Takazudo/zudo-blanks/panels/art-kumiko-void/alternatives/standard/README.md

# Kumiko Void — Standard Alternative

These nine boards form the complete standard Kumiko alternative to the selected wide set in the parent directory. Replace all nine layers together; do not mix standard and wide layers.

The original board IDs are preserved. Color and ENIG sequence match the wide set. This directory is not an instruction to build an additional stack.

| Layer | Original board ID | Mask | Finish |
| ---: | --- | --- | --- |
| 1 | 17-kumiko-void-standard-L01-black-enig-art | black | enig-art |
| 2 | 17-kumiko-void-standard-L02-red-mask-only | red | mask-only |
| 3 | 17-kumiko-void-standard-L03-green-mask-only | green | mask-only |
| 4 | 17-kumiko-void-standard-L04-black-enig-art | black | enig-art |
| 5 | 17-kumiko-void-standard-L05-red-mask-only | red | mask-only |
| 6 | 17-kumiko-void-standard-L06-green-mask-only | green | mask-only |
| 7 | 17-kumiko-void-standard-L07-black-enig-art | black | enig-art |
| 8 | 17-kumiko-void-standard-L08-red-mask-only | red | mask-only |
| 9 | 17-kumiko-void-standard-L09-green-mask-only | green | mask-only |

These files are editable handoff boards. KiCad DRC/CAM, supplier acceptance, quote, and physical-fit checks remain pending.
