Takazudo/zudo-blanks/doc/src/content/docs/catalog/index.mdx

---
title: Panel Catalog
description: Every panel project in the repository, with a source-derived preview.
sidebar_position: 1
---

Browse all 66 panel project directories. Each image is a **KiCad layer rendering** of the committed board source. It is a visual directory aid, not a supplier CAM approval. The five new layered designs and grouped lower packages show every selected board or sheet; open their design pages for the Revision 5 visual concept, interactive 3D preview and fabrication records.

**Release boundary:** Local native DRC and CAM checks cover the five new stacks and grouped lower sheets. Factory CAM review, quotes, finish availability and physical fit remain pending. No purchase or factory acceptance is recorded.

[Five layered designs](../designs/) · [Manufacturing records](../manufacturing/) · [Preview regeneration](../workflow/panel-previews)

## Plain blanks and adapters

20 project directories.

<div className="panel-grid">
<article className="panel-card">
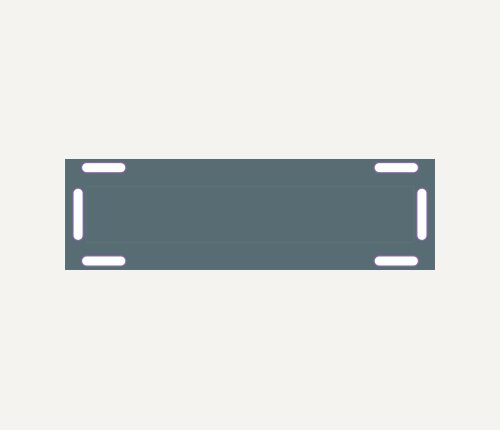
[picture p9: doc/public/assets/panels/alumi-3u-to-1u-v1.png]
KiCad source rendering of Alumi 3U To 1U V1

<h3><a href="https://github.com/Takazudo/zudo-blanks/tree/main/panels/alumi-3u-to-1u-v1">Alumi 3U To 1U V1</a></h3>
<p>Repository design · manufacturing status not established</p>
<small><code>panels/alumi-3u-to-1u-v1</code></small>
</article>
<article className="panel-card">
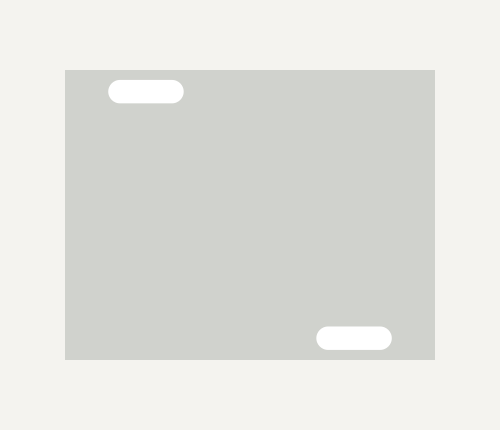
[picture p10: doc/public/assets/panels/alumi-blanks-v1-1U-10hp.png]
KiCad source rendering of Plain 1U · 10 HP

<h3><a href="https://github.com/Takazudo/zudo-blanks/tree/main/panels/alumi-blanks-v1-1U-10hp">Plain 1U · 10 HP</a></h3>
<p>Repository design · manufacturing status not established</p>
<small><code>panels/alumi-blanks-v1-1U-10hp</code></small>
</article>
<article className="panel-card">
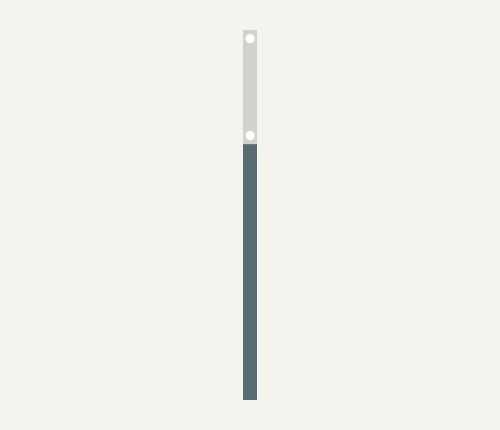
[picture p11: doc/public/assets/panels/alumi-blanks-v1-1U-1hp.png]
KiCad source rendering of Plain 1U · 1 HP

<h3><a href="https://github.com/Takazudo/zudo-blanks/tree/main/panels/alumi-blanks-v1-1U-1hp">Plain 1U · 1 HP</a></h3>
<p>Repository design · manufacturing status not established</p>
<small><code>panels/alumi-blanks-v1-1U-1hp</code></small>
</article>
<article className="panel-card">
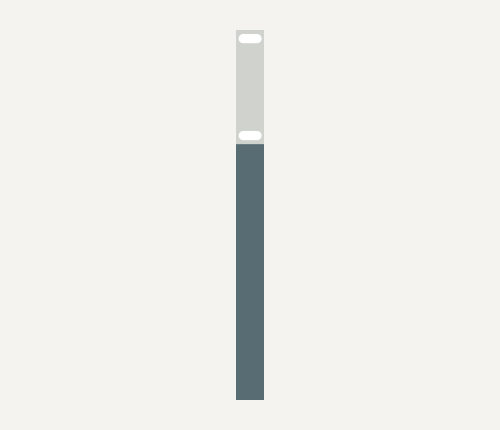
[picture p12: doc/public/assets/panels/alumi-blanks-v1-1U-2hp.png]
KiCad source rendering of Plain 1U · 2 HP

<h3><a href="https://github.com/Takazudo/zudo-blanks/tree/main/panels/alumi-blanks-v1-1U-2hp">Plain 1U · 2 HP</a></h3>
<p>Repository design · manufacturing status not established</p>
<small><code>panels/alumi-blanks-v1-1U-2hp</code></small>
</article>
<article className="panel-card">
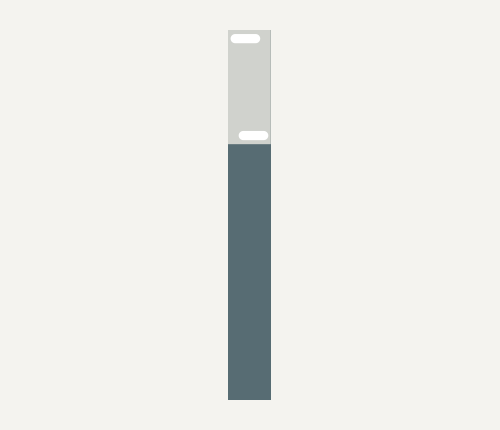
[picture p13: doc/public/assets/panels/alumi-blanks-v1-1U-3hp.png]
KiCad source rendering of Plain 1U · 3 HP

<h3><a href="https://github.com/Takazudo/zudo-blanks/tree/main/panels/alumi-blanks-v1-1U-3hp">Plain 1U · 3 HP</a></h3>
<p>Repository design · manufacturing status not established</p>
<small><code>panels/alumi-blanks-v1-1U-3hp</code></small>
</article>
<article className="panel-card">
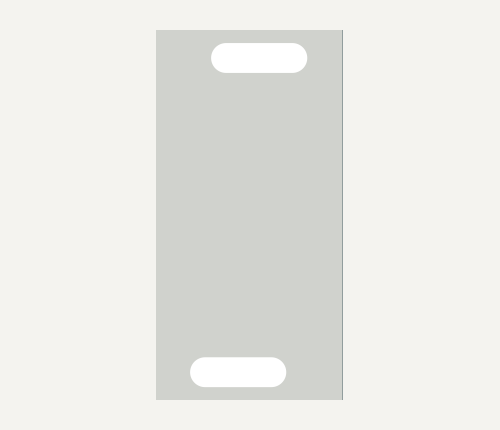
[picture p14: doc/public/assets/panels/alumi-blanks-v1-1U-4hp.png]
KiCad source rendering of Plain 1U · 4 HP

<h3><a href="https://github.com/Takazudo/zudo-blanks/tree/main/panels/alumi-blanks-v1-1U-4hp">Plain 1U · 4 HP</a></h3>
<p>Repository design · manufacturing status not established</p>
<small><code>panels/alumi-blanks-v1-1U-4hp</code></small>
</article>
<article className="panel-card">
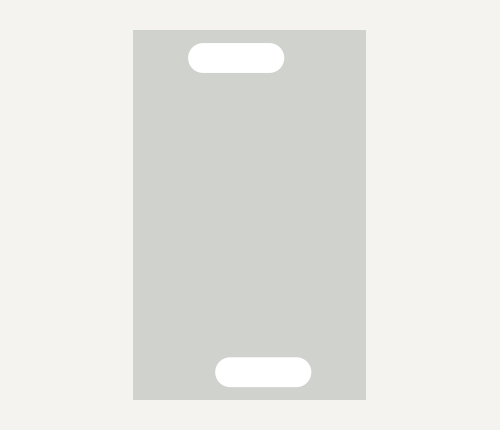
[picture p15: doc/public/assets/panels/alumi-blanks-v1-1U-5hp.png]
KiCad source rendering of Plain 1U · 5 HP

<h3><a href="https://github.com/Takazudo/zudo-blanks/tree/main/panels/alumi-blanks-v1-1U-5hp">Plain 1U · 5 HP</a></h3>
<p>Repository design · manufacturing status not established</p>
<small><code>panels/alumi-blanks-v1-1U-5hp</code></small>
</article>
<article className="panel-card">
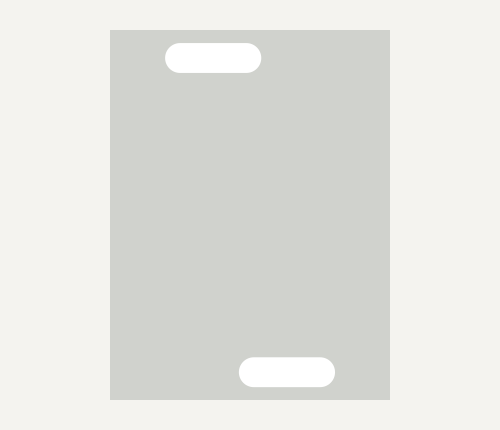
[picture p16: doc/public/assets/panels/alumi-blanks-v1-1U-6hp.png]
KiCad source rendering of Plain 1U · 6 HP

<h3><a href="https://github.com/Takazudo/zudo-blanks/tree/main/panels/alumi-blanks-v1-1U-6hp">Plain 1U · 6 HP</a></h3>
<p>Repository design · manufacturing status not established</p>
<small><code>panels/alumi-blanks-v1-1U-6hp</code></small>
</article>
<article className="panel-card">
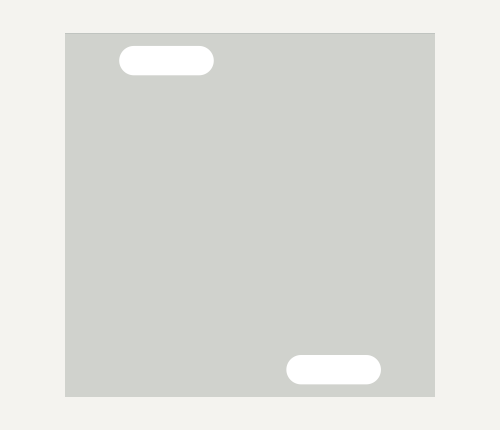
[picture p17: doc/public/assets/panels/alumi-blanks-v1-1U-8hp.png]
KiCad source rendering of Plain 1U · 8 HP

<h3><a href="https://github.com/Takazudo/zudo-blanks/tree/main/panels/alumi-blanks-v1-1U-8hp">Plain 1U · 8 HP</a></h3>
<p>Repository design · manufacturing status not established</p>
<small><code>panels/alumi-blanks-v1-1U-8hp</code></small>
</article>
<article className="panel-card">
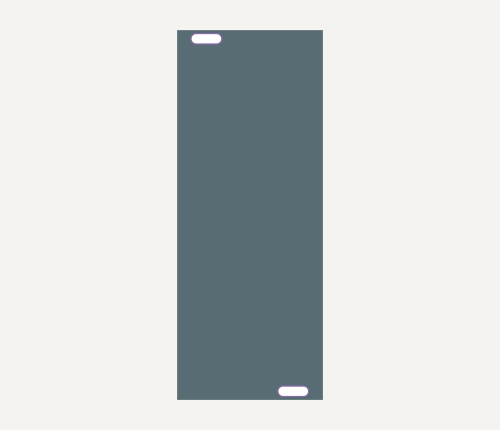
[picture p18: doc/public/assets/panels/alumi-blanks-v1-3U-10hp.png]
KiCad source rendering of Plain 3U · 10 HP

<h3><a href="https://github.com/Takazudo/zudo-blanks/tree/main/panels/alumi-blanks-v1-3U-10hp">Plain 3U · 10 HP</a></h3>
<p>Repository design · manufacturing status not established</p>
<small><code>panels/alumi-blanks-v1-3U-10hp</code></small>
</article>
<article className="panel-card">
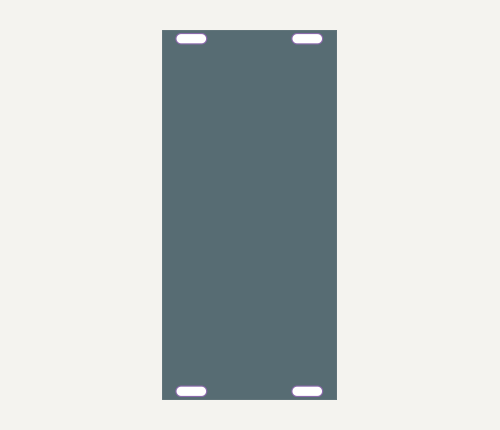
[picture p19: doc/public/assets/panels/alumi-blanks-v1-3U-12hp.png]
KiCad source rendering of Plain 3U · 12 HP

<h3><a href="https://github.com/Takazudo/zudo-blanks/tree/main/panels/alumi-blanks-v1-3U-12hp">Plain 3U · 12 HP</a></h3>
<p>Repository design · manufacturing status not established</p>
<small><code>panels/alumi-blanks-v1-3U-12hp</code></small>
</article>
<article className="panel-card">
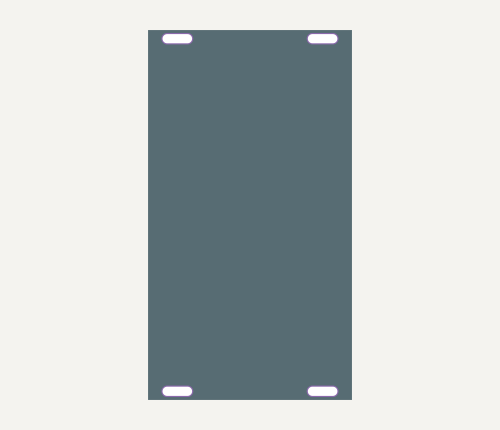
[picture p20: doc/public/assets/panels/alumi-blanks-v1-3U-14hp.png]
KiCad source rendering of Plain 3U · 14 HP

<h3><a href="https://github.com/Takazudo/zudo-blanks/tree/main/panels/alumi-blanks-v1-3U-14hp">Plain 3U · 14 HP</a></h3>
<p>Repository design · manufacturing status not established</p>
<small><code>panels/alumi-blanks-v1-3U-14hp</code></small>
</article>
<article className="panel-card">
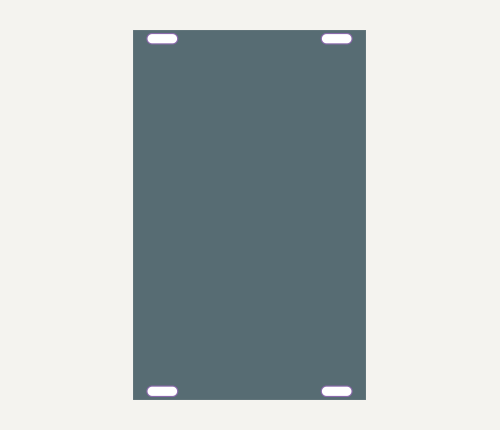
[picture p21: doc/public/assets/panels/alumi-blanks-v1-3U-16hp.png]
KiCad source rendering of Plain 3U · 16 HP

<h3><a href="https://github.com/Takazudo/zudo-blanks/tree/main/panels/alumi-blanks-v1-3U-16hp">Plain 3U · 16 HP</a></h3>
<p>Repository design · manufacturing status not established</p>
<small><code>panels/alumi-blanks-v1-3U-16hp</code></small>
</article>
<article className="panel-card">
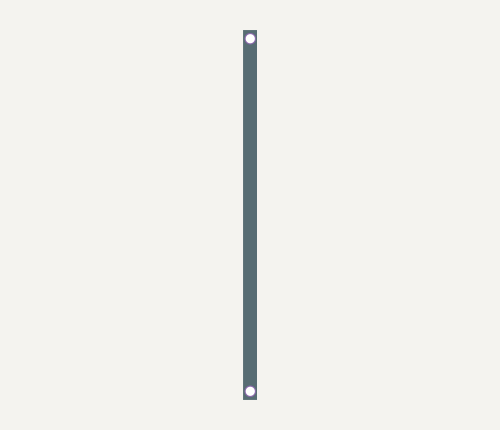
[picture p22: doc/public/assets/panels/alumi-blanks-v1-3U-1hp.png]
KiCad source rendering of Plain 3U · 1 HP

<h3><a href="https://github.com/Takazudo/zudo-blanks/tree/main/panels/alumi-blanks-v1-3U-1hp">Plain 3U · 1 HP</a></h3>
<p>Repository design · manufacturing status not established</p>
<small><code>panels/alumi-blanks-v1-3U-1hp</code></small>
</article>
<article className="panel-card">
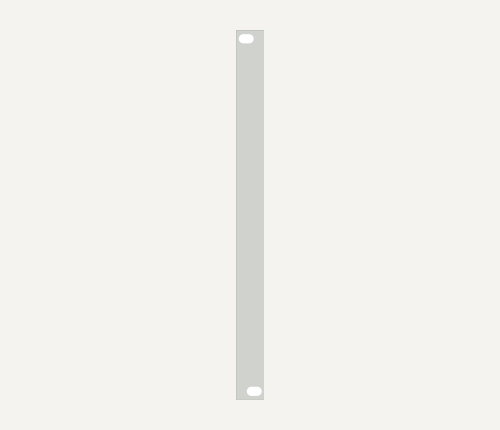
[picture p23: doc/public/assets/panels/alumi-blanks-v1-3U-2hp.png]
KiCad source rendering of Plain 3U · 2 HP

<h3><a href="https://github.com/Takazudo/zudo-blanks/tree/main/panels/alumi-blanks-v1-3U-2hp">Plain 3U · 2 HP</a></h3>
<p>Repository design · manufacturing status not established</p>
<small><code>panels/alumi-blanks-v1-3U-2hp</code></small>
</article>
<article className="panel-card">
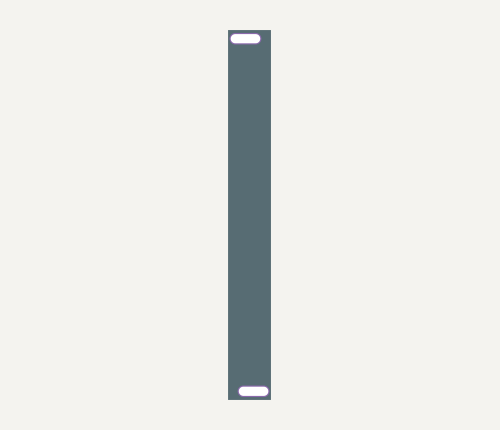
[picture p24: doc/public/assets/panels/alumi-blanks-v1-3U-3hp.png]
KiCad source rendering of Plain 3U · 3 HP

<h3><a href="https://github.com/Takazudo/zudo-blanks/tree/main/panels/alumi-blanks-v1-3U-3hp">Plain 3U · 3 HP</a></h3>
<p>Repository design · manufacturing status not established</p>
<small><code>panels/alumi-blanks-v1-3U-3hp</code></small>
</article>
<article className="panel-card">
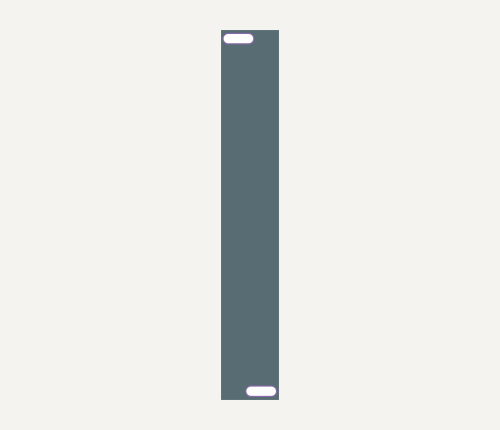
[picture p25: doc/public/assets/panels/alumi-blanks-v1-3U-4hp.png]
KiCad source rendering of Plain 3U · 4 HP

<h3><a href="https://github.com/Takazudo/zudo-blanks/tree/main/panels/alumi-blanks-v1-3U-4hp">Plain 3U · 4 HP</a></h3>
<p>Repository design · manufacturing status not established</p>
<small><code>panels/alumi-blanks-v1-3U-4hp</code></small>
</article>
<article className="panel-card">
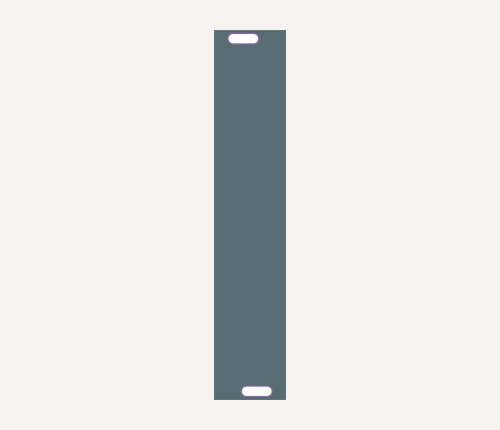
[picture p26: doc/public/assets/panels/alumi-blanks-v1-3U-5hp.png]
KiCad source rendering of Plain 3U · 5 HP

<h3><a href="https://github.com/Takazudo/zudo-blanks/tree/main/panels/alumi-blanks-v1-3U-5hp">Plain 3U · 5 HP</a></h3>
<p>Repository design · manufacturing status not established</p>
<small><code>panels/alumi-blanks-v1-3U-5hp</code></small>
</article>
<article className="panel-card">
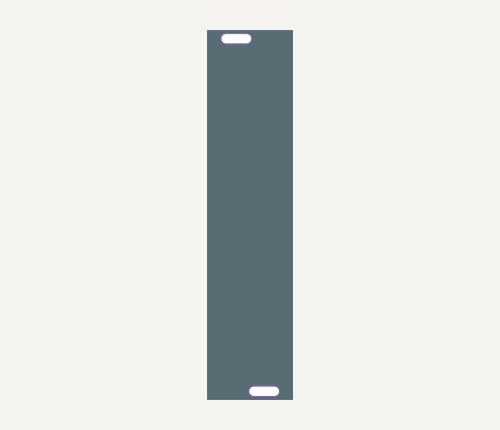
[picture p27: doc/public/assets/panels/alumi-blanks-v1-3U-6hp.png]
KiCad source rendering of Plain 3U · 6 HP

<h3><a href="https://github.com/Takazudo/zudo-blanks/tree/main/panels/alumi-blanks-v1-3U-6hp">Plain 3U · 6 HP</a></h3>
<p>Repository design · manufacturing status not established</p>
<small><code>panels/alumi-blanks-v1-3U-6hp</code></small>
</article>
<article className="panel-card">
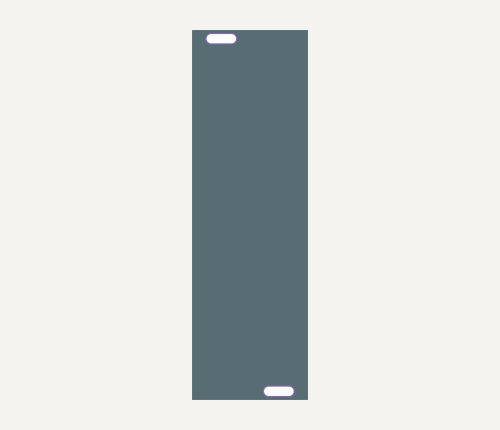
[picture p28: doc/public/assets/panels/alumi-blanks-v1-3U-8hp.png]
KiCad source rendering of Plain 3U · 8 HP

<h3><a href="https://github.com/Takazudo/zudo-blanks/tree/main/panels/alumi-blanks-v1-3U-8hp">Plain 3U · 8 HP</a></h3>
<p>Repository design · manufacturing status not established</p>
<small><code>panels/alumi-blanks-v1-3U-8hp</code></small>
</article>
</div>

## Side frames

5 project directories.

<div className="panel-grid">
<article className="panel-card">
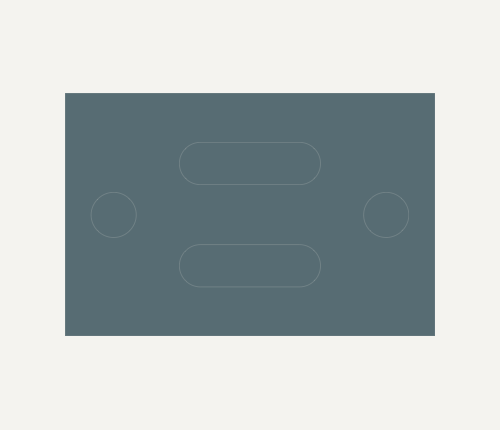
[picture p29: doc/public/assets/panels/zb-side-frame-1u.png]
KiCad source rendering of Zb Side Frame 1U

<h3><a href="https://github.com/Takazudo/zudo-blanks/tree/main/panels/zb-side-frame-1u">Zb Side Frame 1U</a></h3>
<p>Repository design · manufacturing status not established</p>
<small><code>panels/zb-side-frame-1u</code></small>
</article>
<article className="panel-card">
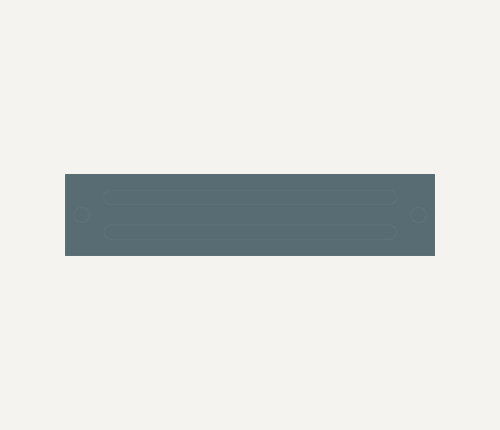
[picture p30: doc/public/assets/panels/zb-side-frame-3u.png]
KiCad source rendering of Zb Side Frame 3U

<h3><a href="https://github.com/Takazudo/zudo-blanks/tree/main/panels/zb-side-frame-3u">Zb Side Frame 3U</a></h3>
<p>Repository design · manufacturing status not established</p>
<small><code>panels/zb-side-frame-3u</code></small>
</article>
<article className="panel-card">
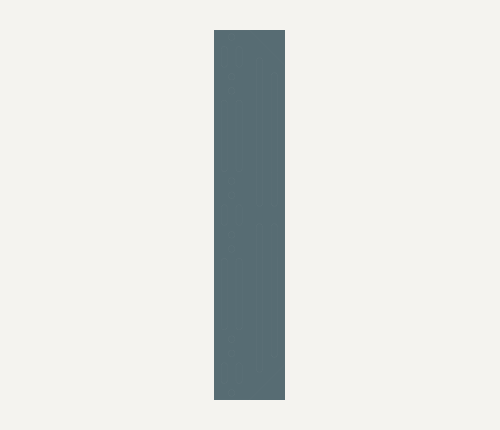
[picture p31: doc/public/assets/panels/zb-side-frame-7u.png]
KiCad source rendering of Zb Side Frame 7U

<h3><a href="https://github.com/Takazudo/zudo-blanks/tree/main/panels/zb-side-frame-7u">Zb Side Frame 7U</a></h3>
<p>Repository design · manufacturing status not established</p>
<small><code>panels/zb-side-frame-7u</code></small>
</article>
<article className="panel-card">
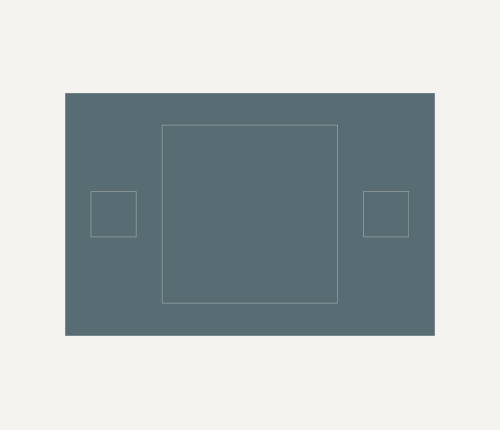
[picture p32: doc/public/assets/panels/zb-side-frame-pad-1u.png]
KiCad source rendering of Zb Side Frame Pad 1U

<h3><a href="https://github.com/Takazudo/zudo-blanks/tree/main/panels/zb-side-frame-pad-1u">Zb Side Frame Pad 1U</a></h3>
<p>Repository design · manufacturing status not established</p>
<small><code>panels/zb-side-frame-pad-1u</code></small>
</article>
<article className="panel-card">
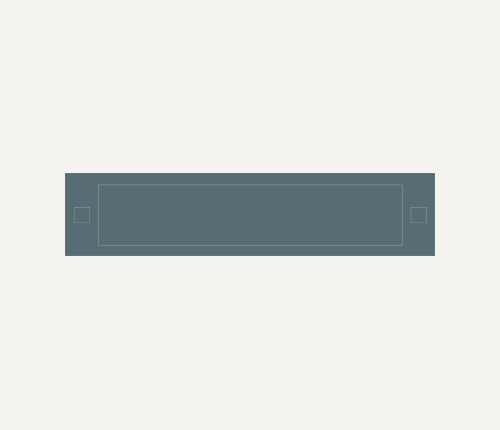
[picture p33: doc/public/assets/panels/zb-side-frame-pad-3u.png]
KiCad source rendering of Zb Side Frame Pad 3U

<h3><a href="https://github.com/Takazudo/zudo-blanks/tree/main/panels/zb-side-frame-pad-3u">Zb Side Frame Pad 3U</a></h3>
<p>Repository design · manufacturing status not established</p>
<small><code>panels/zb-side-frame-pad-3u</code></small>
</article>
</div>

## Artwork and layered designs

11 project directories.

<div className="panel-grid">
<article className="panel-card">
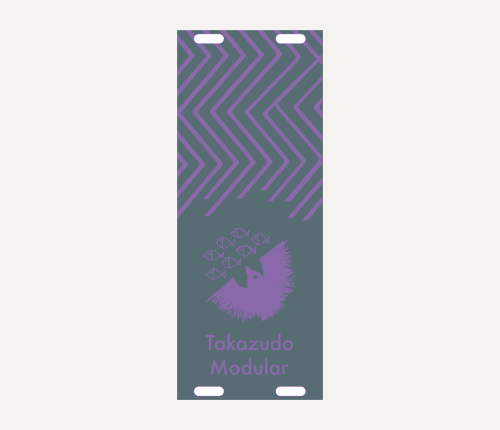
[picture p34: doc/public/assets/panels/art-10hp-takazudo-modular.png]
KiCad source rendering of 10Hp Takazudo Modular

<h3><a href="https://github.com/Takazudo/zudo-blanks/tree/main/panels/art-10hp-takazudo-modular">10Hp Takazudo Modular</a></h3>
<p>Repository design · manufacturing status not established</p>
<small><code>panels/art-10hp-takazudo-modular</code></small>
</article>
<article className="panel-card">
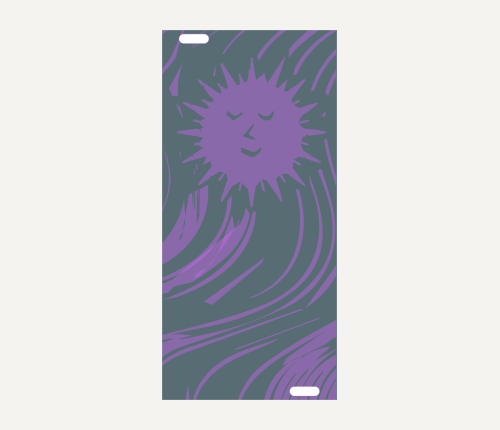
[picture p35: doc/public/assets/panels/art-12hp-sun.png]
KiCad source rendering of 12Hp Sun

<h3><a href="https://github.com/Takazudo/zudo-blanks/tree/main/panels/art-12hp-sun">12Hp Sun</a></h3>
<p>Repository design · manufacturing status not established</p>
<small><code>panels/art-12hp-sun</code></small>
</article>
<article className="panel-card">
<a href="https://github.com/Takazudo/zudo-blanks/tree/main/panels/art-coral-vault">KiCad source rendering of Coral Vault</a>
<h3><a href="https://github.com/Takazudo/zudo-blanks/tree/main/panels/art-coral-vault">Coral Vault</a></h3>
<p>8 selected layers · local native DRC/CAM checked · factory review pending</p>
<small><code>panels/art-coral-vault</code></small>
</article>
<article className="panel-card">
<a href="https://github.com/Takazudo/zudo-blanks/tree/main/panels/art-fault-line">KiCad source rendering of Fault Line</a>
<h3><a href="https://github.com/Takazudo/zudo-blanks/tree/main/panels/art-fault-line">Fault Line</a></h3>
<p>9 selected layers · local native DRC/CAM checked · factory review pending</p>
<small><code>panels/art-fault-line</code></small>
</article>
<article className="panel-card">
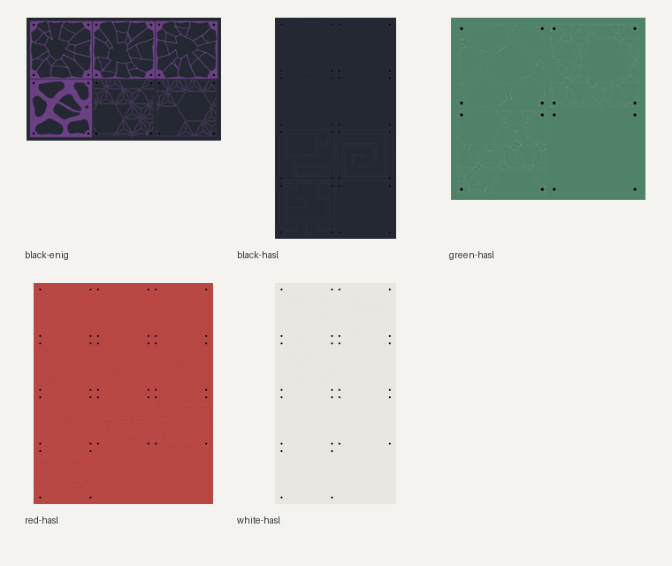
[picture p36: doc/public/assets/panels/art-grouped-lowers.png]
KiCad source rendering of Grouped Lowers

<h3><a href="https://github.com/Takazudo/zudo-blanks/tree/main/panels/art-grouped-lowers">Grouped Lowers</a></h3>
<p>5 grouped sheets · local native DRC/CAM checked · factory review pending</p>
<small><code>panels/art-grouped-lowers</code></small>
</article>
<article className="panel-card">
<a href="https://github.com/Takazudo/zudo-blanks/tree/main/panels/art-kumiko-void">KiCad source rendering of Kumiko Void</a>
<h3><a href="https://github.com/Takazudo/zudo-blanks/tree/main/panels/art-kumiko-void">Kumiko Void</a></h3>
<p>9 selected layers · local native DRC/CAM checked · factory review pending</p>
<small><code>panels/art-kumiko-void</code></small>
</article>
<article className="panel-card">
<a href="https://github.com/Takazudo/zudo-blanks/tree/main/panels/art-spider-nest">KiCad source rendering of Spider Nest</a>
<h3><a href="https://github.com/Takazudo/zudo-blanks/tree/main/panels/art-spider-nest">Spider Nest</a></h3>
<p>8 selected layers · local native DRC/CAM checked · factory review pending</p>
<small><code>panels/art-spider-nest</code></small>
</article>
<article className="panel-card">
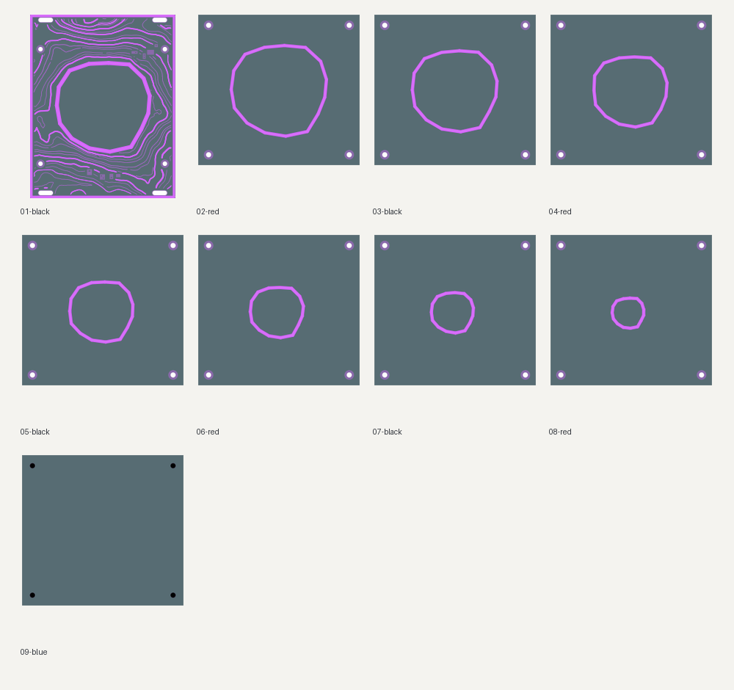
[picture p37: doc/public/assets/panels/art-strip-mine.png]
KiCad source rendering of Strip Mine

<h3><a href="https://github.com/Takazudo/zudo-blanks/tree/main/panels/art-strip-mine">Strip Mine</a></h3>
<p>9 layered source boards · historical project status</p>
<small><code>panels/art-strip-mine</code></small>
</article>
<article className="panel-card">
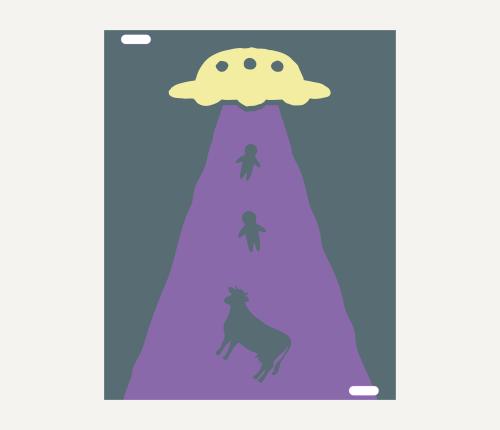
[picture p38: doc/public/assets/panels/art-ufo.png]
KiCad source rendering of Ufo

<h3><a href="https://github.com/Takazudo/zudo-blanks/tree/main/panels/art-ufo">Ufo</a></h3>
<p>Repository design · manufacturing status not established</p>
<small><code>panels/art-ufo</code></small>
</article>
<article className="panel-card">
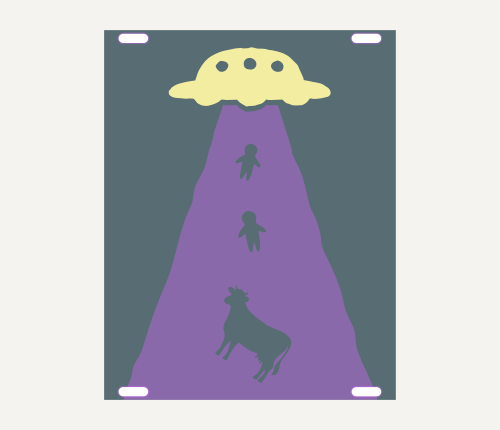
[picture p39: doc/public/assets/panels/art-ufo-v2.png]
KiCad source rendering of Ufo V2

<h3><a href="https://github.com/Takazudo/zudo-blanks/tree/main/panels/art-ufo-v2">Ufo V2</a></h3>
<p>Repository design · manufacturing status not established</p>
<small><code>panels/art-ufo-v2</code></small>
</article>
<article className="panel-card">
<a href="https://github.com/Takazudo/zudo-blanks/tree/main/panels/art-woven-maze">KiCad source rendering of Woven Maze</a>
<h3><a href="https://github.com/Takazudo/zudo-blanks/tree/main/panels/art-woven-maze">Woven Maze</a></h3>
<p>9 selected layers · local native DRC/CAM checked · factory review pending</p>
<small><code>panels/art-woven-maze</code></small>
</article>
</div>

## Saucer series

30 project directories.

<div className="panel-grid">
<article className="panel-card">
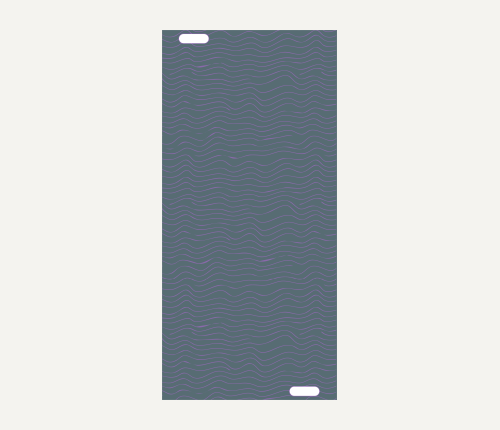
[picture p40: doc/public/assets/panels/saucer1-slow-wave-12hp.png]
KiCad source rendering of Saucer 1 · Slow Wave · 12 HP

<h3><a href="https://github.com/Takazudo/zudo-blanks/tree/main/panels/saucer1-slow-wave-12hp">Saucer 1 · Slow Wave · 12 HP</a></h3>
<p>Repository design · manufacturing status not established</p>
<small><code>panels/saucer1-slow-wave-12hp</code></small>
</article>
<article className="panel-card">
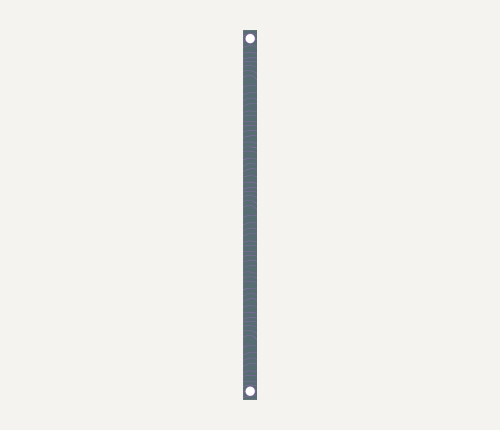
[picture p41: doc/public/assets/panels/saucer1-slow-wave-1hp.png]
KiCad source rendering of Saucer 1 · Slow Wave · 1 HP

<h3><a href="https://github.com/Takazudo/zudo-blanks/tree/main/panels/saucer1-slow-wave-1hp">Saucer 1 · Slow Wave · 1 HP</a></h3>
<p>Repository design · manufacturing status not established</p>
<small><code>panels/saucer1-slow-wave-1hp</code></small>
</article>
<article className="panel-card">
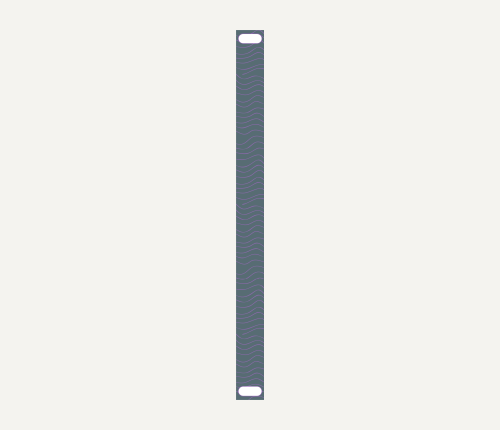
[picture p42: doc/public/assets/panels/saucer1-slow-wave-2hp.png]
KiCad source rendering of Saucer 1 · Slow Wave · 2 HP

<h3><a href="https://github.com/Takazudo/zudo-blanks/tree/main/panels/saucer1-slow-wave-2hp">Saucer 1 · Slow Wave · 2 HP</a></h3>
<p>Repository design · manufacturing status not established</p>
<small><code>panels/saucer1-slow-wave-2hp</code></small>
</article>
<article className="panel-card">
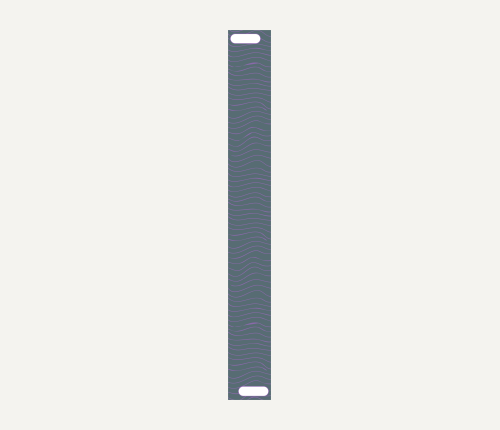
[picture p43: doc/public/assets/panels/saucer1-slow-wave-3hp.png]
KiCad source rendering of Saucer 1 · Slow Wave · 3 HP

<h3><a href="https://github.com/Takazudo/zudo-blanks/tree/main/panels/saucer1-slow-wave-3hp">Saucer 1 · Slow Wave · 3 HP</a></h3>
<p>Repository design · manufacturing status not established</p>
<small><code>panels/saucer1-slow-wave-3hp</code></small>
</article>
<article className="panel-card">
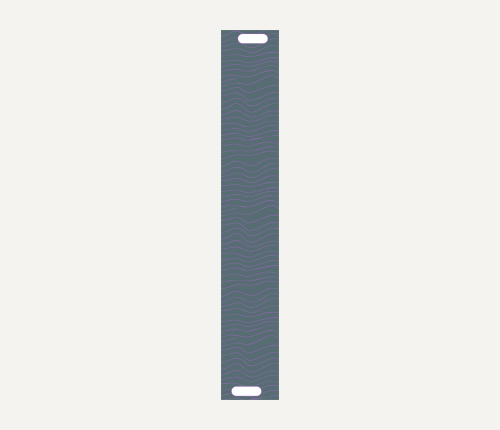
[picture p44: doc/public/assets/panels/saucer1-slow-wave-4hp.png]
KiCad source rendering of Saucer 1 · Slow Wave · 4 HP

<h3><a href="https://github.com/Takazudo/zudo-blanks/tree/main/panels/saucer1-slow-wave-4hp">Saucer 1 · Slow Wave · 4 HP</a></h3>
<p>Repository design · manufacturing status not established</p>
<small><code>panels/saucer1-slow-wave-4hp</code></small>
</article>
<article className="panel-card">
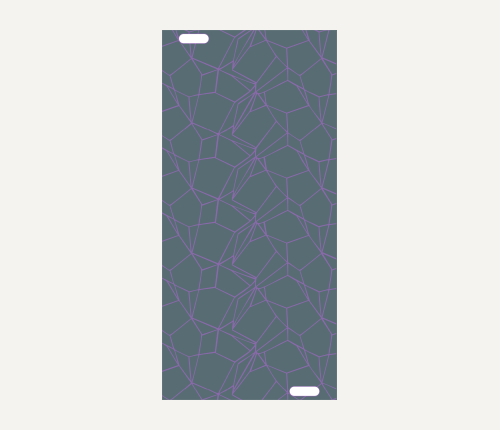
[picture p45: doc/public/assets/panels/saucer2-crystal-flow-12hp.png]
KiCad source rendering of Saucer 2 · Crystal Flow · 12 HP

<h3><a href="https://github.com/Takazudo/zudo-blanks/tree/main/panels/saucer2-crystal-flow-12hp">Saucer 2 · Crystal Flow · 12 HP</a></h3>
<p>Repository design · manufacturing status not established</p>
<small><code>panels/saucer2-crystal-flow-12hp</code></small>
</article>
<article className="panel-card">
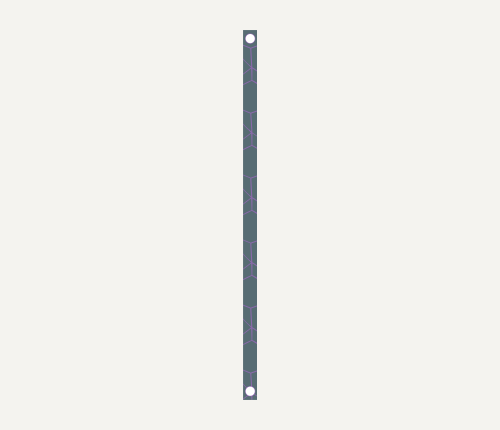
[picture p46: doc/public/assets/panels/saucer2-crystal-flow-1hp.png]
KiCad source rendering of Saucer 2 · Crystal Flow · 1 HP

<h3><a href="https://github.com/Takazudo/zudo-blanks/tree/main/panels/saucer2-crystal-flow-1hp">Saucer 2 · Crystal Flow · 1 HP</a></h3>
<p>Repository design · manufacturing status not established</p>
<small><code>panels/saucer2-crystal-flow-1hp</code></small>
</article>
<article className="panel-card">
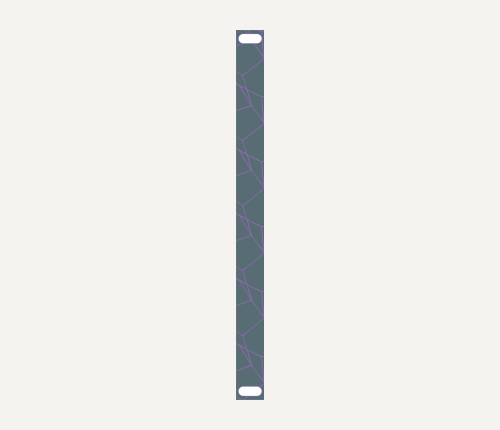
[picture p47: doc/public/assets/panels/saucer2-crystal-flow-2hp.png]
KiCad source rendering of Saucer 2 · Crystal Flow · 2 HP

<h3><a href="https://github.com/Takazudo/zudo-blanks/tree/main/panels/saucer2-crystal-flow-2hp">Saucer 2 · Crystal Flow · 2 HP</a></h3>
<p>Repository design · manufacturing status not established</p>
<small><code>panels/saucer2-crystal-flow-2hp</code></small>
</article>
<article className="panel-card">
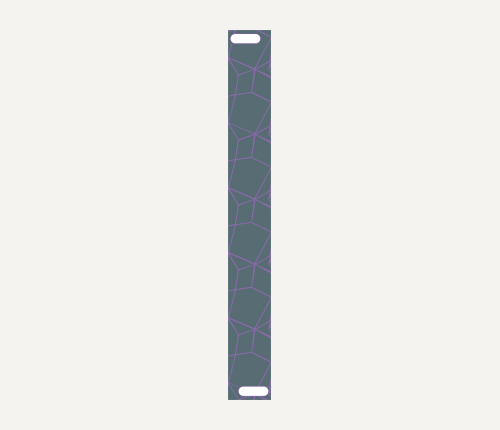
[picture p48: doc/public/assets/panels/saucer2-crystal-flow-3hp.png]
KiCad source rendering of Saucer 2 · Crystal Flow · 3 HP

<h3><a href="https://github.com/Takazudo/zudo-blanks/tree/main/panels/saucer2-crystal-flow-3hp">Saucer 2 · Crystal Flow · 3 HP</a></h3>
<p>Repository design · manufacturing status not established</p>
<small><code>panels/saucer2-crystal-flow-3hp</code></small>
</article>
<article className="panel-card">
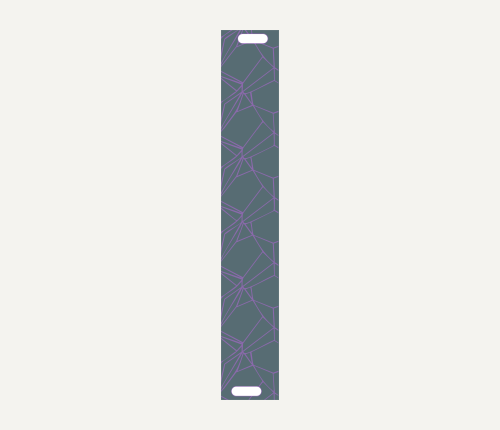
[picture p49: doc/public/assets/panels/saucer2-crystal-flow-4hp.png]
KiCad source rendering of Saucer 2 · Crystal Flow · 4 HP

<h3><a href="https://github.com/Takazudo/zudo-blanks/tree/main/panels/saucer2-crystal-flow-4hp">Saucer 2 · Crystal Flow · 4 HP</a></h3>
<p>Repository design · manufacturing status not established</p>
<small><code>panels/saucer2-crystal-flow-4hp</code></small>
</article>
<article className="panel-card">
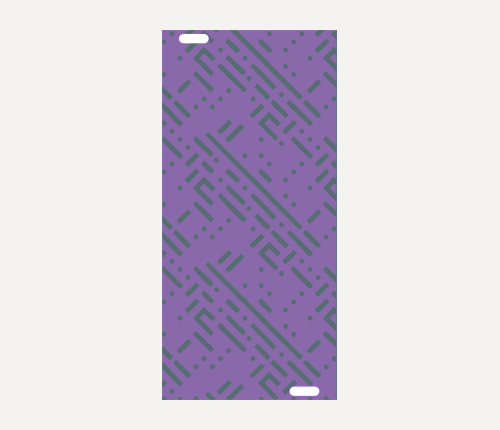
[picture p50: doc/public/assets/panels/saucer3-grid-play-12hp.png]
KiCad source rendering of Saucer 3 · Grid Play · 12 HP

<h3><a href="https://github.com/Takazudo/zudo-blanks/tree/main/panels/saucer3-grid-play-12hp">Saucer 3 · Grid Play · 12 HP</a></h3>
<p>Repository design · manufacturing status not established</p>
<small><code>panels/saucer3-grid-play-12hp</code></small>
</article>
<article className="panel-card">
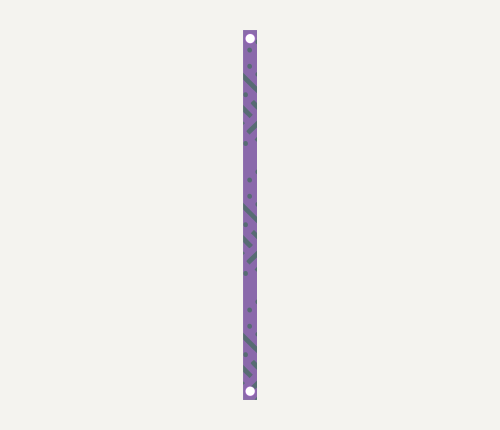
[picture p51: doc/public/assets/panels/saucer3-grid-play-1hp.png]
KiCad source rendering of Saucer 3 · Grid Play · 1 HP

<h3><a href="https://github.com/Takazudo/zudo-blanks/tree/main/panels/saucer3-grid-play-1hp">Saucer 3 · Grid Play · 1 HP</a></h3>
<p>Repository design · manufacturing status not established</p>
<small><code>panels/saucer3-grid-play-1hp</code></small>
</article>
<article className="panel-card">
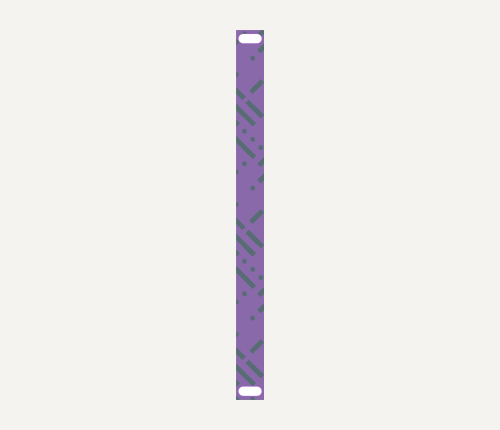
[picture p52: doc/public/assets/panels/saucer3-grid-play-2hp.png]
KiCad source rendering of Saucer 3 · Grid Play · 2 HP

<h3><a href="https://github.com/Takazudo/zudo-blanks/tree/main/panels/saucer3-grid-play-2hp">Saucer 3 · Grid Play · 2 HP</a></h3>
<p>Repository design · manufacturing status not established</p>
<small><code>panels/saucer3-grid-play-2hp</code></small>
</article>
<article className="panel-card">
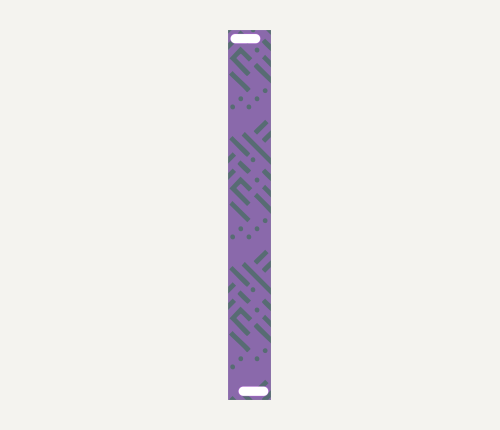
[picture p53: doc/public/assets/panels/saucer3-grid-play-3hp.png]
KiCad source rendering of Saucer 3 · Grid Play · 3 HP

<h3><a href="https://github.com/Takazudo/zudo-blanks/tree/main/panels/saucer3-grid-play-3hp">Saucer 3 · Grid Play · 3 HP</a></h3>
<p>Repository design · manufacturing status not established</p>
<small><code>panels/saucer3-grid-play-3hp</code></small>
</article>
<article className="panel-card">
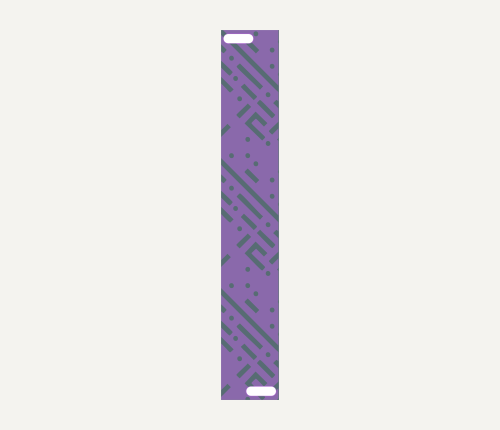
[picture p54: doc/public/assets/panels/saucer3-grid-play-4hp.png]
KiCad source rendering of Saucer 3 · Grid Play · 4 HP

<h3><a href="https://github.com/Takazudo/zudo-blanks/tree/main/panels/saucer3-grid-play-4hp">Saucer 3 · Grid Play · 4 HP</a></h3>
<p>Repository design · manufacturing status not established</p>
<small><code>panels/saucer3-grid-play-4hp</code></small>
</article>
<article className="panel-card">
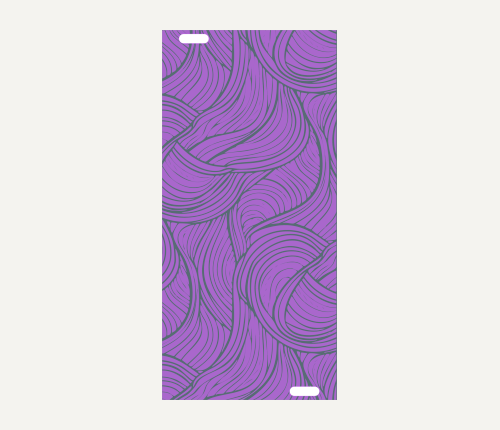
[picture p55: doc/public/assets/panels/saucer4-streamlines-12hp.png]
KiCad source rendering of Saucer 4 · Streamlines · 12 HP

<h3><a href="https://github.com/Takazudo/zudo-blanks/tree/main/panels/saucer4-streamlines-12hp">Saucer 4 · Streamlines · 12 HP</a></h3>
<p>Repository design · manufacturing status not established</p>
<small><code>panels/saucer4-streamlines-12hp</code></small>
</article>
<article className="panel-card">
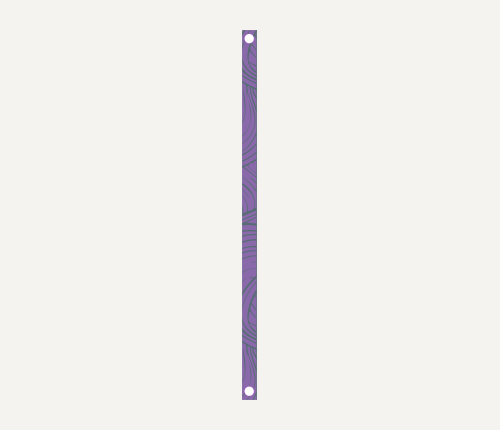
[picture p56: doc/public/assets/panels/saucer4-streamlines-1hp.png]
KiCad source rendering of Saucer 4 · Streamlines · 1 HP

<h3><a href="https://github.com/Takazudo/zudo-blanks/tree/main/panels/saucer4-streamlines-1hp">Saucer 4 · Streamlines · 1 HP</a></h3>
<p>Repository design · manufacturing status not established</p>
<small><code>panels/saucer4-streamlines-1hp</code></small>
</article>
<article className="panel-card">
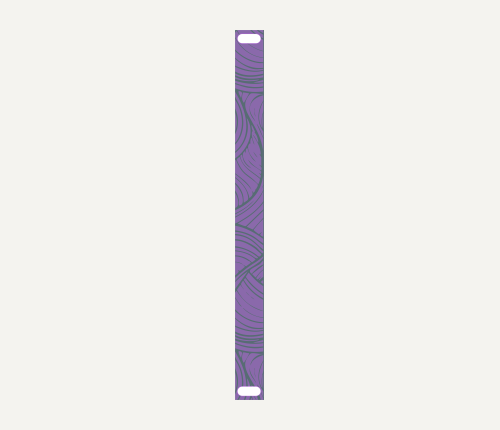
[picture p57: doc/public/assets/panels/saucer4-streamlines-2hp.png]
KiCad source rendering of Saucer 4 · Streamlines · 2 HP

<h3><a href="https://github.com/Takazudo/zudo-blanks/tree/main/panels/saucer4-streamlines-2hp">Saucer 4 · Streamlines · 2 HP</a></h3>
<p>Repository design · manufacturing status not established</p>
<small><code>panels/saucer4-streamlines-2hp</code></small>
</article>
<article className="panel-card">
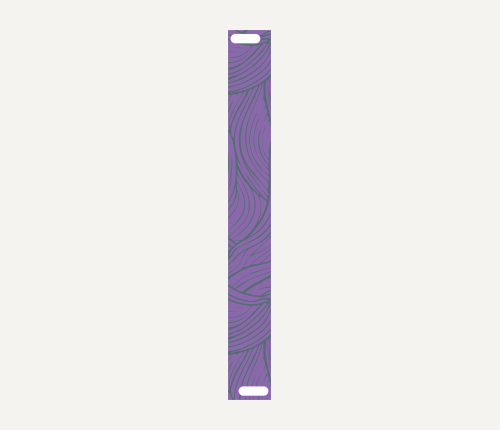
[picture p58: doc/public/assets/panels/saucer4-streamlines-3hp.png]
KiCad source rendering of Saucer 4 · Streamlines · 3 HP

<h3><a href="https://github.com/Takazudo/zudo-blanks/tree/main/panels/saucer4-streamlines-3hp">Saucer 4 · Streamlines · 3 HP</a></h3>
<p>Repository design · manufacturing status not established</p>
<small><code>panels/saucer4-streamlines-3hp</code></small>
</article>
<article className="panel-card">
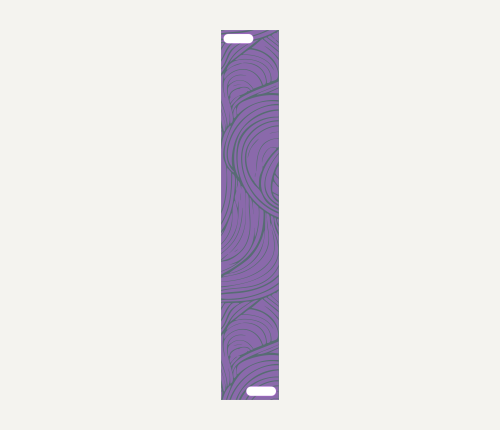
[picture p59: doc/public/assets/panels/saucer4-streamlines-4hp.png]
KiCad source rendering of Saucer 4 · Streamlines · 4 HP

<h3><a href="https://github.com/Takazudo/zudo-blanks/tree/main/panels/saucer4-streamlines-4hp">Saucer 4 · Streamlines · 4 HP</a></h3>
<p>Repository design · manufacturing status not established</p>
<small><code>panels/saucer4-streamlines-4hp</code></small>
</article>
<article className="panel-card">
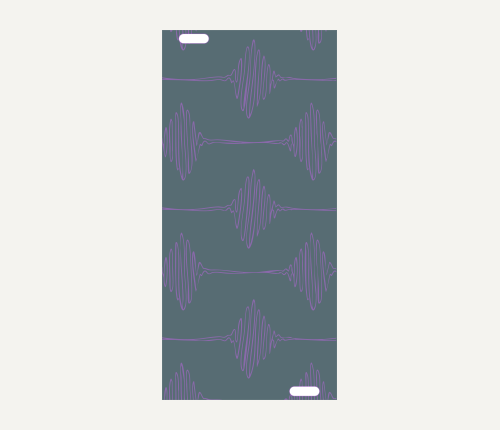
[picture p60: doc/public/assets/panels/saucer5-rhythm-wave-12hp.png]
KiCad source rendering of Saucer 5 · Rhythm Wave · 12 HP

<h3><a href="https://github.com/Takazudo/zudo-blanks/tree/main/panels/saucer5-rhythm-wave-12hp">Saucer 5 · Rhythm Wave · 12 HP</a></h3>
<p>Repository design · manufacturing status not established</p>
<small><code>panels/saucer5-rhythm-wave-12hp</code></small>
</article>
<article className="panel-card">
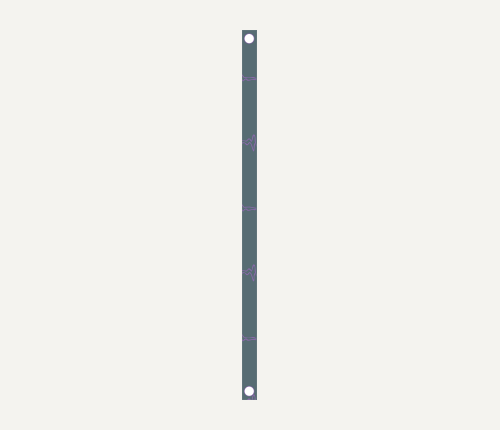
[picture p61: doc/public/assets/panels/saucer5-rhythm-wave-1hp.png]
KiCad source rendering of Saucer 5 · Rhythm Wave · 1 HP

<h3><a href="https://github.com/Takazudo/zudo-blanks/tree/main/panels/saucer5-rhythm-wave-1hp">Saucer 5 · Rhythm Wave · 1 HP</a></h3>
<p>Repository design · manufacturing status not established</p>
<small><code>panels/saucer5-rhythm-wave-1hp</code></small>
</article>
<article className="panel-card">
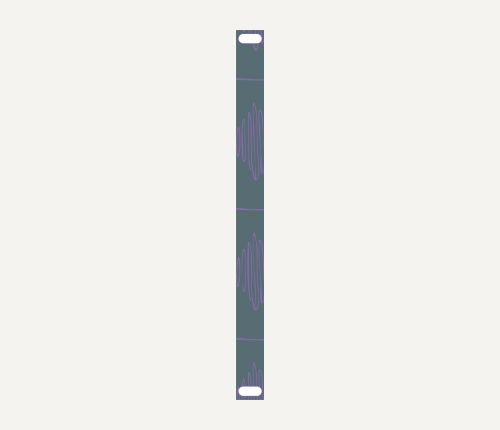
[picture p62: doc/public/assets/panels/saucer5-rhythm-wave-2hp.png]
KiCad source rendering of Saucer 5 · Rhythm Wave · 2 HP

<h3><a href="https://github.com/Takazudo/zudo-blanks/tree/main/panels/saucer5-rhythm-wave-2hp">Saucer 5 · Rhythm Wave · 2 HP</a></h3>
<p>Repository design · manufacturing status not established</p>
<small><code>panels/saucer5-rhythm-wave-2hp</code></small>
</article>
<article className="panel-card">
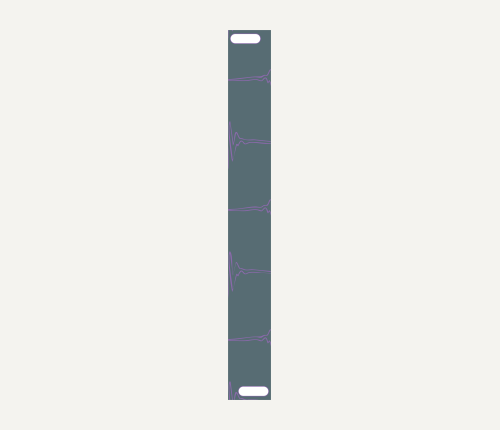
[picture p63: doc/public/assets/panels/saucer5-rhythm-wave-3hp.png]
KiCad source rendering of Saucer 5 · Rhythm Wave · 3 HP

<h3><a href="https://github.com/Takazudo/zudo-blanks/tree/main/panels/saucer5-rhythm-wave-3hp">Saucer 5 · Rhythm Wave · 3 HP</a></h3>
<p>Repository design · manufacturing status not established</p>
<small><code>panels/saucer5-rhythm-wave-3hp</code></small>
</article>
<article className="panel-card">
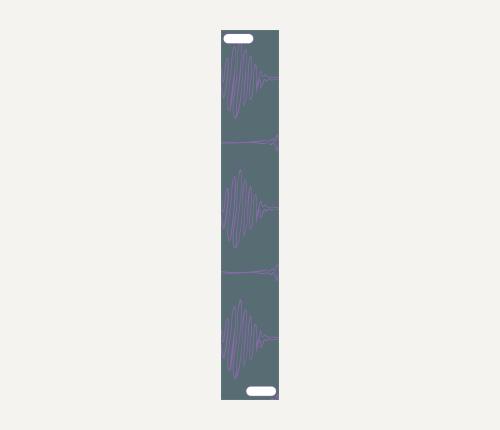
[picture p64: doc/public/assets/panels/saucer5-rhythm-wave-4hp.png]
KiCad source rendering of Saucer 5 · Rhythm Wave · 4 HP

<h3><a href="https://github.com/Takazudo/zudo-blanks/tree/main/panels/saucer5-rhythm-wave-4hp">Saucer 5 · Rhythm Wave · 4 HP</a></h3>
<p>Repository design · manufacturing status not established</p>
<small><code>panels/saucer5-rhythm-wave-4hp</code></small>
</article>
<article className="panel-card">
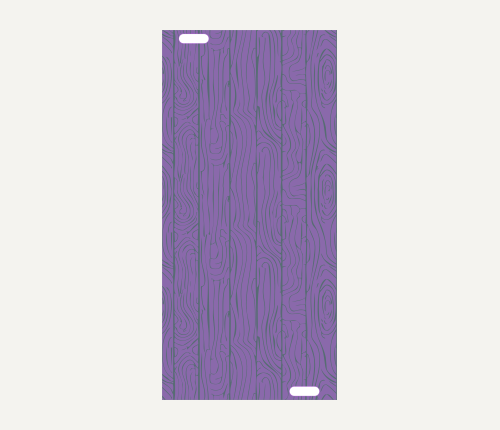
[picture p65: doc/public/assets/panels/saucer6-grainscape-12hp.png]
KiCad source rendering of Saucer 6 · Grainscape · 12 HP

<h3><a href="https://github.com/Takazudo/zudo-blanks/tree/main/panels/saucer6-grainscape-12hp">Saucer 6 · Grainscape · 12 HP</a></h3>
<p>Repository design · manufacturing status not established</p>
<small><code>panels/saucer6-grainscape-12hp</code></small>
</article>
<article className="panel-card">
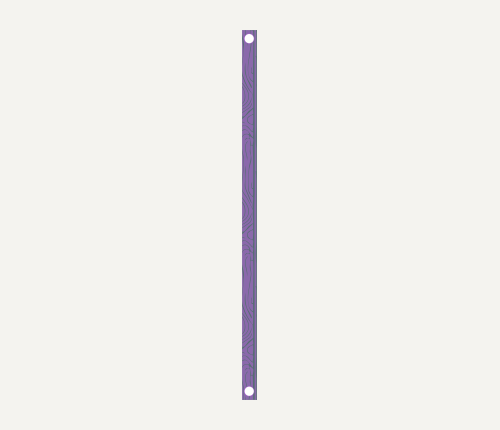
[picture p66: doc/public/assets/panels/saucer6-grainscape-1hp.png]
KiCad source rendering of Saucer 6 · Grainscape · 1 HP

<h3><a href="https://github.com/Takazudo/zudo-blanks/tree/main/panels/saucer6-grainscape-1hp">Saucer 6 · Grainscape · 1 HP</a></h3>
<p>Repository design · manufacturing status not established</p>
<small><code>panels/saucer6-grainscape-1hp</code></small>
</article>
<article className="panel-card">
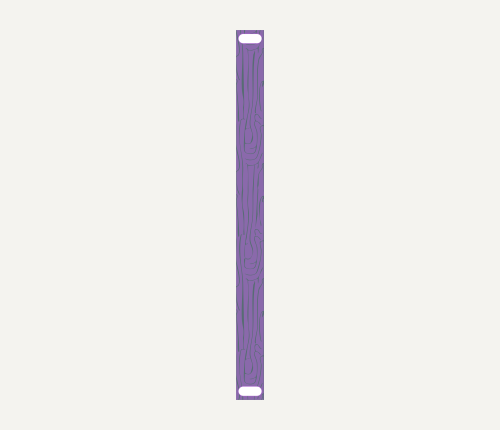
[picture p67: doc/public/assets/panels/saucer6-grainscape-2hp.png]
KiCad source rendering of Saucer 6 · Grainscape · 2 HP

<h3><a href="https://github.com/Takazudo/zudo-blanks/tree/main/panels/saucer6-grainscape-2hp">Saucer 6 · Grainscape · 2 HP</a></h3>
<p>Repository design · manufacturing status not established</p>
<small><code>panels/saucer6-grainscape-2hp</code></small>
</article>
<article className="panel-card">
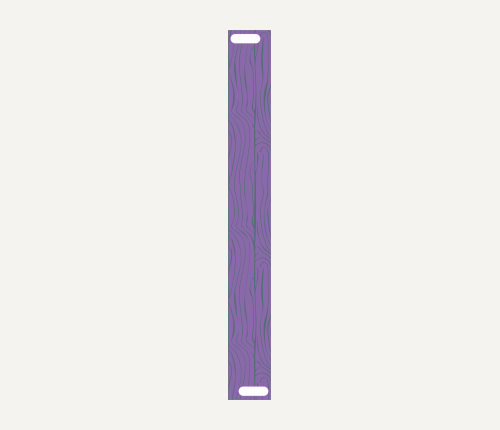
[picture p68: doc/public/assets/panels/saucer6-grainscape-3hp.png]
KiCad source rendering of Saucer 6 · Grainscape · 3 HP

<h3><a href="https://github.com/Takazudo/zudo-blanks/tree/main/panels/saucer6-grainscape-3hp">Saucer 6 · Grainscape · 3 HP</a></h3>
<p>Repository design · manufacturing status not established</p>
<small><code>panels/saucer6-grainscape-3hp</code></small>
</article>
<article className="panel-card">
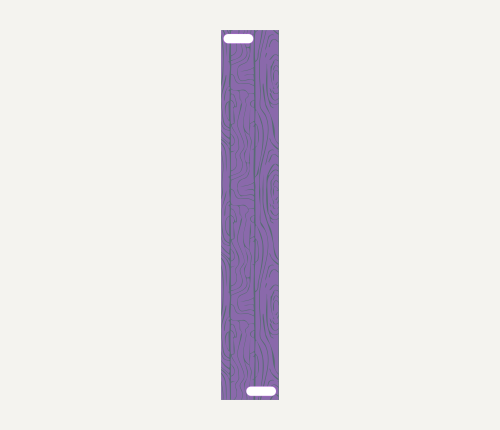
[picture p69: doc/public/assets/panels/saucer6-grainscape-4hp.png]
KiCad source rendering of Saucer 6 · Grainscape · 4 HP

<h3><a href="https://github.com/Takazudo/zudo-blanks/tree/main/panels/saucer6-grainscape-4hp">Saucer 6 · Grainscape · 4 HP</a></h3>
<p>Repository design · manufacturing status not established</p>
<small><code>panels/saucer6-grainscape-4hp</code></small>
</article>
</div>
