Takazudo/zudo-blanks/doc/src/content/docs/engineering/index.mdx

---
title: Engineering
sidebar_position: 3
---

The Revision 5 model defines visual intent; the selected native KiCad boards incorporate locally reviewed process adjustments. Read [source of truth](./source-of-truth.mdx) before regenerating or comparing layers.

<CategoryNav category="engineering" />
