Takazudo/zudo-blanks/doc/src/content/docs/misc/index.mdx

---
title: Additional Resources
sidebar_position: 1
---

The earlier miscellaneous route is retained. Current resources are organized under the [panel catalog](../catalog/), [design references](../overview/references.mdx), [manufacturing records](../manufacturing/) and [KiCad how-to guides](../how-to/).
