Takazudo/zudo-blanks/doc/src/content/docs/workflow/index.mdx

---
title: Workflow
sidebar_position: 6
---

For a new board, begin with the [KiCad workflow](../how-to/kicad-workflow.md), then update the [source-derived panel catalog](./panel-previews.mdx). For the selected layered art projects, read the [source-of-truth guide](../engineering/source-of-truth.mdx) and [manufacturing status](../manufacturing/) before changing native or visual geometry.

<CategoryNav category="workflow" />
