Takazudo/zudo-blanks/artwork-resources/pcb-art/docs-overlay/src/content/docs/designs/index.mdx

---
title: "Five Designs"
description: "Layer order, colors, openings, and finish intent by design."
sidebar_position: 2
---

The five design homes retain original board IDs, front-to-back layer order, and the selected finish metadata.

<CategoryNav category="designs" />
