Takazudo/zudo-blanks/artwork-resources/pcb-art/docs-overlay/src/content/docs/overview/index.mdx

---
title: "Overview"
description: "Revision 5 design decisions, history, and current handoff status."
sidebar_position: 1
---

The five layered designs share one source geometry and finish policy, with separate native boards and review records.

<CategoryNav category="overview" />
