Takazudo/zudo-blanks/artwork-resources/pcb-art/docs-overlay/src/content/docs/handoff/references.mdx

---
title: "References and Source Dates"
description: "Original design, software, and process sources noted by the handoff."
sidebar_position: 4
---

## Site framework

The incoming documentation notes were prepared against the zudo-doc pages checked on 2026-09-24 UTC. Software guidance may change, so confirm current package versions and CLI behavior before site work.

| Reference | Topic |
| --- | --- |
| [Installation](https://zudo-doc.takazudomodular.com/docs/getting-started/installation/) | Node, pnpm, and project initialization |
| [create-zudo-doc CLI](https://zudo-doc.takazudomodular.com/docs/reference/create-zudo-doc/) | New project options |
| [Configuration](https://zudo-doc.takazudomodular.com/docs/guides/configuration/) | Site config, home page, and header navigation |
| [Writing Docs](https://zudo-doc.takazudomodular.com/docs/getting-started/writing-docs/) | MDX and frontmatter |
| [Structuring Navigations](https://zudo-doc.takazudomodular.com/docs/getting-started/structuring-navigations/) | Categories and navigation |

The incoming source bibliography is preserved in documentation/RESEARCH_SOURCES.json. Examples from other projects were reviewed as references; project-specific deployment settings were not imported.

## Design references

- [Strip Mine](https://github.com/Takazudo/zudo-blanks/tree/main/panels/art-strip-mine) is the layered-panel predecessor.
- [Strip Mine preview](https://github.com/Takazudo/zudo-blanks/tree/main/panels/art-strip-mine/preview) supplies dimensions and stack context.
- [Favites pentagona](https://www.coralsoftheworld.org/species_factsheets/species_factsheet_summary/favites-pentagona/) and [Smithsonian Ocean: Corals and Coral Reefs](https://ocean.si.edu/ocean-life/invertebrates/corals-and-coral-reefs) informed the abstract coral forms.

## Process references

The source work cited [KiCad board format](https://dev-docs.kicad.org/en/file-formats/sexpr-pcb/), [KiCad common graphics and pads](https://dev-docs.kicad.org/en/file-formats/sexpr-intro/), [JLCPCB capabilities](https://jlcpcb.com/capabilities/pcb-capabilities), [surface finishes](https://jlcpcb.com/help/article/jlcpcb-surface-finish), and [NPTH design guidance](https://jlcpcb.com/blog/npth-design-guide). Recheck current supplier rules and quote conditions before using them. A source citation is not a supplier acceptance result.

The project dimensions and layer sequence come from the included geometry generator and manifests, not from external reference images.
