Takazudo/zudo-blanks/artwork-resources/pcb-art/docs-overlay/src/content/docs/handoff/resources.mdx

---
title: "Files and Resources"
description: "Where the geometry, boards, images, and evidence live."
sidebar_position: 3
---

## Repository sources

| Path | Contents |
| --- | --- |
| panels/art-* | 43 selected native boards and nine standard Kumiko alternatives |
| artwork-resources/pcb-art/preview-source | Geometry and offline viewer generator |
| artwork-resources/pcb-art/pcb/manifest.json and manifest.csv | Original IDs, layer, mask, finish, and repo board path |
| artwork-resources/pcb-art/resources/images | Curated preview and comparison images, retained once |
| artwork-resources/pcb-art/resources/reference | Original design references |
| artwork-resources/pcb-art/resources/manufacturing-review | Marked Kumiko and artwork gap references |
| artwork-resources/pcb-art/resources/order | Draft quantity and hardware inputs |
| artwork-resources/pcb-art/validation and reports | Compact geometry and export evidence |
| artwork-resources/pcb-art/tools | Geometry export and local-review helpers |
| artwork-resources/pcb-art/docs-overlay/src/content/docs | Curated source pages for later site work |

Original design IDs distinguish 43 selected boards from 52 total records across both Kumiko variants. See IMPORT_MANIFEST.json for all imported, transformed, deduplicated, and omitted source paths.

## Regenerate the preview

The viewer HTML is generated by the command in preview-source/README.md. The preview-source/dist directory is ignored. Image references from preview-source/docs and docs-overlay/public are retained once under resources/images.

## Use vector outputs

The default generated/rev5-export/resources/vector directory is ignored. Generate vectors from canonical geometry and use layer-specific Edge_Cuts, Drill, F.Cu, and F.Mask files only with their documented semantics. Do not use the rendered front.svg as routed cut data. Native NPTH pads already define functional holes.

The documentation source references /assets/pcb-art paths expected in a future site build. The site asset tree is generated during that separate migration; it is not duplicated in this import.
