Takazudo/zudo-blanks/artwork-resources/pcb-art/docs-overlay/src/content/docs/handoff/zudo-doc.mdx

---
title: "Future zudo-doc Site Work"
description: "Imported page and config sources for a later site migration."
sidebar_position: 1
---

The incoming handoff includes English-curated MDX pages and a starter configuration. It does not include the zudo-doc framework or installed dependencies, and this source import has not initialized, migrated, or built the repository documentation site.

The source design targeted Node.js 22 or later and pnpm at the time its references were checked. Confirm current official setup commands before site work. Use a new project directory or carefully merge the pages and config into the existing site; preserve its existing routes and dependencies.

The retained page tree has overview, designs, engineering, manufacturing, assembly, and handoff categories. Its image and preview links resolve to generated public assets that must be materialized from the canonical resource directories during the future site migration.
