Takazudo/zudo-blanks/artwork-resources/pcb-art/resources/reference/coral-vault-initial.png

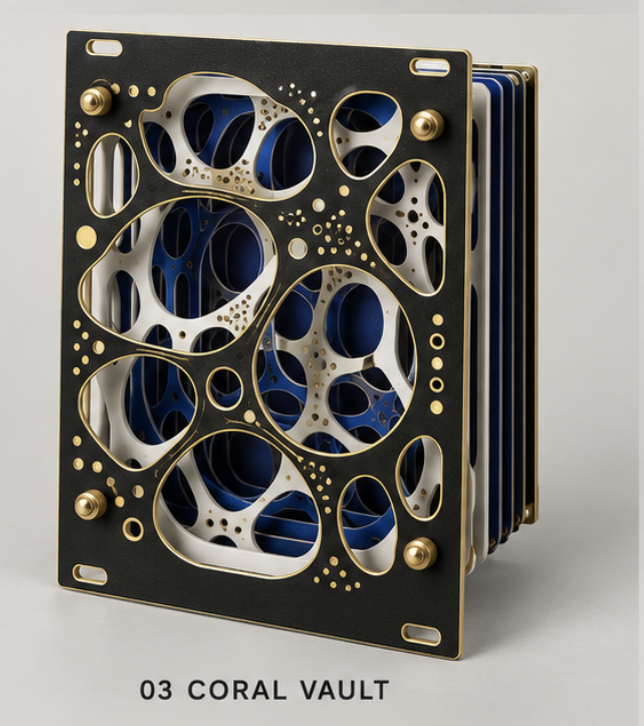
artwork-resources/pcb-art/resources/reference/coral-vault-initial.png
