Takazudo/zudo-blanks/artwork-resources/pcb-art/resources/reference/fault-line-initial.png

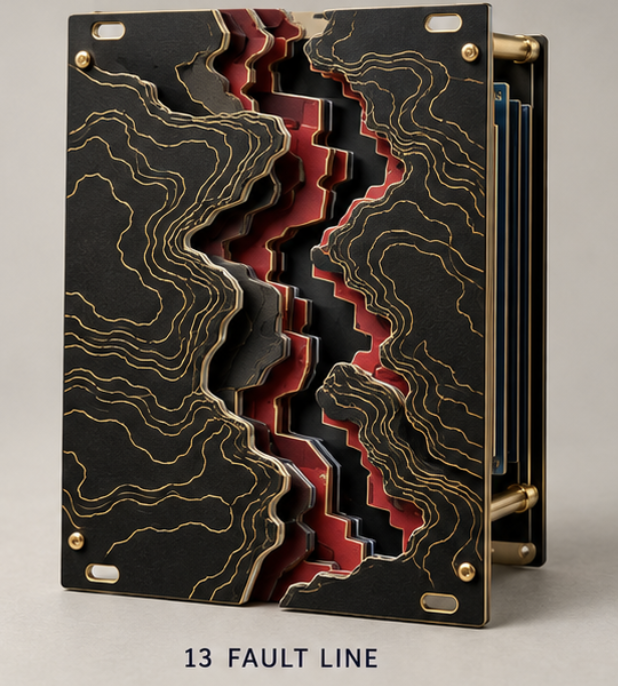
artwork-resources/pcb-art/resources/reference/fault-line-initial.png
