Takazudo/zudo-blanks/artwork-resources/pcb-art/resources/reference/spider-nest-initial.png

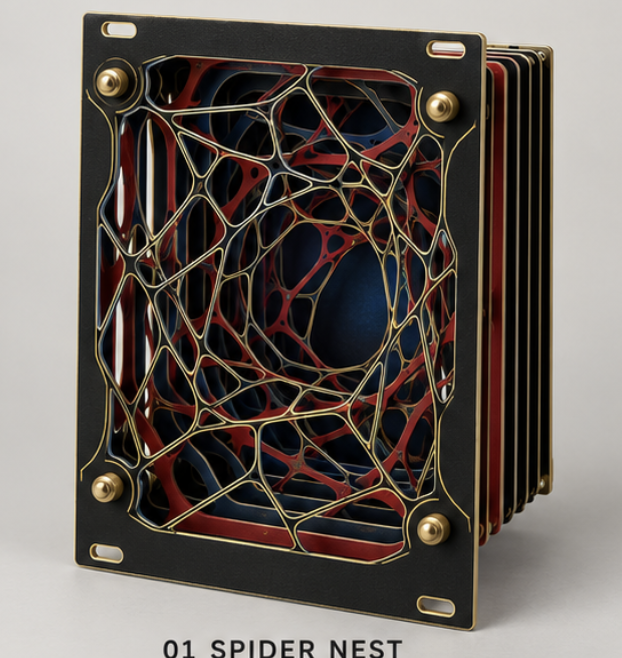
artwork-resources/pcb-art/resources/reference/spider-nest-initial.png
