Takazudo/zudo-blanks/order-packages/four-art-series/current/bundle/README.md

# Four-series order candidates

Choose one alternative in variants/*/ORDER.md. Never purchase all ZIPs.

34 byte-identical native sources, fresh DRC/CAM and previews are included. Blue score overlays mark full-span V-scores, not routed cuts. Stack-side images are nominal geometry, not physical-fit evidence.

Quoted prices are unknown. Factory CAM/scoring, perforated sheet handling, edge appearance and physical fit remain pending. Native verification does not establish factory approval or savings.

Verify SHA256SUMS and receipt.json after download using the checked-in --verify-bundle command.
