Takazudo/zudo-blanks/order-packages/four-art-series/current/bundle/variants/split-red/ORDER.md

# split-red order candidate

Choose ONE alternative. Purchase only the ZIPs listed in this table; individual reference exports in the bundle are not additional orders.

| Package | Kind | Color / finish | mm | Designs | Quantity | Produced | Blank cells | Surplus | ZIP |
| --- | --- | --- | --- | ---: | ---: | ---: | ---: | ---: | --- |
| lower-panel-white-hasl | scored_lower_grid | white / lead-free HASL | 111.3 × 292.9 | 3 | 25 | 75 | 0 | 0 | [lower-panel-white-hasl.zip](../../variants/split-red/cam/lower-panel-white-hasl.zip) |
| lower-panel-black-enig | scored_lower_grid | black / ENIG | 313.9 × 198.6 | 6 | 25 | 150 | 0 | 0 | [lower-panel-black-enig.zip](../../variants/split-red/cam/lower-panel-black-enig.zip) |
| lower-panel-green-hasl | scored_lower_grid | green / lead-free HASL | 212.6 × 198.6 | 4 | 25 | 100 | 0 | 0 | [lower-panel-green-hasl.zip](../../variants/split-red/cam/lower-panel-green-hasl.zip) |
| 03-coral-vault-L03-purple-mask-only | routed_lower_singleton | purple / lead-free HASL | 101.3 × 94.3 | 1 | 25 | 25 | 0 | 0 | [03-coral-vault-L03-purple-mask-only.zip](../../packages/03-coral-vault-L03-purple-mask-only.zip) |
| 03-coral-vault-L06-yellow-mask-only | routed_lower_singleton | yellow / lead-free HASL | 101.3 × 94.3 | 1 | 25 | 25 | 0 | 0 | [03-coral-vault-L06-yellow-mask-only.zip](../../packages/03-coral-vault-L06-yellow-mask-only.zip) |
| 03-coral-vault-L08-blue-mask-only | routed_lower_singleton | blue / lead-free HASL | 101.3 × 94.3 | 1 | 25 | 25 | 0 | 0 | [03-coral-vault-L08-blue-mask-only.zip](../../packages/03-coral-vault-L08-blue-mask-only.zip) |
| lower-panel-black-hasl | scored_lower_grid | black / lead-free HASL | 212.6 × 198.6 | 4 | 25 | 100 | 0 | 0 | [lower-panel-black-hasl.zip](../../variants/split-red/cam/lower-panel-black-hasl.zip) |
| lower-panel-red-hasl-six | scored_lower_grid | red / lead-free HASL | 212.6 × 292.9 | 6 | 25 | 150 | 0 | 0 | [lower-panel-red-hasl-six.zip](../../variants/split-red/cam/lower-panel-red-hasl-six.zip) |
| lower-panel-red-hasl-fault | scored_lower_grid | red / lead-free HASL | 212.6 × 198.6 | 4 | 25 | 100 | 0 | 0 | [lower-panel-red-hasl-fault.zip](../../variants/split-red/cam/lower-panel-red-hasl-fault.zip) |
| 01-spider-nest-L01-black-enig-art | routed_standalone_top | black / ENIG | 101.3 × 128.5 | 1 | 25 | 25 | 0 | 0 | [01-spider-nest-L01-black-enig-art.zip](../../packages/01-spider-nest-L01-black-enig-art.zip) |
| 03-coral-vault-L01-black-enig-art | routed_standalone_top | black / ENIG | 101.3 × 128.5 | 1 | 25 | 25 | 0 | 0 | [03-coral-vault-L01-black-enig-art.zip](../../packages/03-coral-vault-L01-black-enig-art.zip) |
| 13-fault-line-L01-black-enig-art | routed_standalone_top | black / ENIG | 101.3 × 128.5 | 1 | 25 | 25 | 0 | 0 | [13-fault-line-L01-black-enig-art.zip](../../packages/13-fault-line-L01-black-enig-art.zip) |
| 17-kumiko-void-wide-L01-black-enig-art | routed_standalone_top | black / ENIG | 101.3 × 128.5 | 1 | 25 | 25 | 0 | 0 | [17-kumiko-void-wide-L01-black-enig-art.zip](../../packages/17-kumiko-void-wide-L01-black-enig-art.zip) |

| Package | Source member IDs | Copies of each member per sheet |
| --- | --- | ---: |
| lower-panel-white-hasl | 01-spider-nest-L02-white-mask-only, 01-spider-nest-L04-white-mask-only, 01-spider-nest-L06-white-mask-only | 1 |
| lower-panel-black-enig | 01-spider-nest-L03-gold-enig-fill, 01-spider-nest-L05-gold-enig-fill, 01-spider-nest-L07-gold-enig-fill, 03-coral-vault-L04-gold-enig-fill, 17-kumiko-void-wide-L04-black-enig-art, 17-kumiko-void-wide-L07-black-enig-art | 1 |
| lower-panel-green-hasl | 03-coral-vault-L02-green-mask-only, 17-kumiko-void-wide-L03-green-mask-only, 17-kumiko-void-wide-L06-green-mask-only, 17-kumiko-void-wide-L09-green-mask-only | 1 |
| 03-coral-vault-L03-purple-mask-only | 03-coral-vault-L03-purple-mask-only | 1 |
| 03-coral-vault-L06-yellow-mask-only | 03-coral-vault-L06-yellow-mask-only | 1 |
| 03-coral-vault-L08-blue-mask-only | 03-coral-vault-L08-blue-mask-only | 1 |
| lower-panel-black-hasl | 13-fault-line-L03-black-mask-only, 13-fault-line-L05-black-mask-only, 13-fault-line-L07-black-mask-only, 13-fault-line-L09-black-mask-only | 1 |
| lower-panel-red-hasl-six | 01-spider-nest-L08-red-mask-only, 03-coral-vault-L05-red-mask-only, 03-coral-vault-L07-red-mask-only, 17-kumiko-void-wide-L02-red-mask-only, 17-kumiko-void-wide-L05-red-mask-only, 17-kumiko-void-wide-L08-red-mask-only | 1 |
| lower-panel-red-hasl-fault | 13-fault-line-L02-red-mask-only, 13-fault-line-L04-red-mask-only, 13-fault-line-L06-red-mask-only, 13-fault-line-L08-red-mask-only | 1 |
| 01-spider-nest-L01-black-enig-art | 01-spider-nest-L01-black-enig-art | 1 |
| 03-coral-vault-L01-black-enig-art | 03-coral-vault-L01-black-enig-art | 1 |
| 13-fault-line-L01-black-enig-art | 13-fault-line-L01-black-enig-art | 1 |
| 17-kumiko-void-wide-L01-black-enig-art | 17-kumiko-void-wide-L01-black-enig-art | 1 |

Requested: 100 stacks / 850 useful pieces. Complete-set supply: 100. Surplus: 0. Blank cells exclude rails and routed cutouts.

All packages: FR-4, 1.6 mm, 2 copper layers, 1 oz; no silkscreen, solder paste or plated holes. Each member occurs once per sheet. Exact member IDs, per-ID surplus, source/config and verification references are in order.json.

Prices, engineering/design fees, routing/scoring, ENIG/area effects, shipping and tax: **unknown**. No dated quote. Factory CAM/scoring, sheet handling and physical fit are pending. Fewer sheets do not prove savings.
