Takazudo/zudo-blanks/order-packages/four-art-series/current/bundle/previews/01-spider-nest-L01-black-enig-art.png

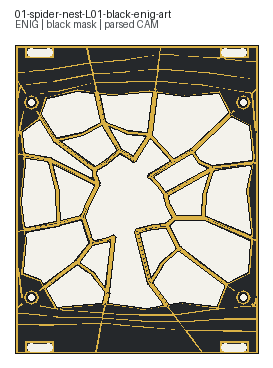
order-packages/four-art-series/current/bundle/previews/01-spider-nest-L01-black-enig-art.png
