Takazudo/zudo-blanks/order-packages/four-art-series/current/bundle/previews/01-spider-nest-L03-gold-enig-fill.png

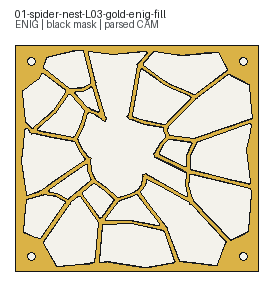
order-packages/four-art-series/current/bundle/previews/01-spider-nest-L03-gold-enig-fill.png
