Takazudo/zudo-blanks/order-packages/four-art-series/current/bundle/previews/01-spider-nest-L06-white-mask-only.png

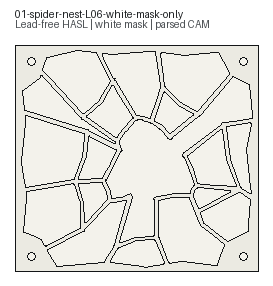
order-packages/four-art-series/current/bundle/previews/01-spider-nest-L06-white-mask-only.png
