Takazudo/zudo-blanks/order-packages/four-art-series/current/bundle/previews/01-spider-nest-L07-gold-enig-fill.png

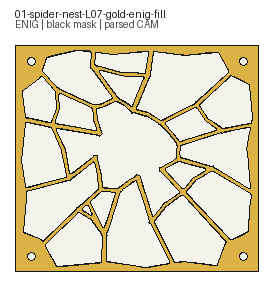
order-packages/four-art-series/current/bundle/previews/01-spider-nest-L07-gold-enig-fill.png
