Takazudo/zudo-blanks/order-packages/four-art-series/current/bundle/previews/03-coral-vault-L01-black-enig-art.png

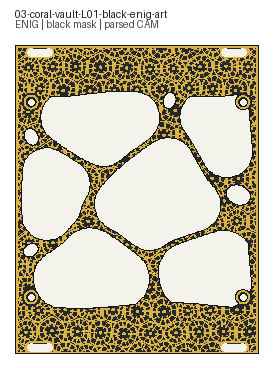
order-packages/four-art-series/current/bundle/previews/03-coral-vault-L01-black-enig-art.png
