Takazudo/zudo-blanks/order-packages/four-art-series/current/bundle/previews/03-coral-vault-L04-gold-enig-fill.png

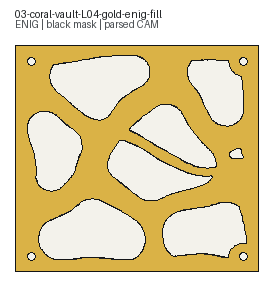
order-packages/four-art-series/current/bundle/previews/03-coral-vault-L04-gold-enig-fill.png
