Takazudo/zudo-blanks/order-packages/four-art-series/current/bundle/previews/03-coral-vault-L05-red-mask-only.png

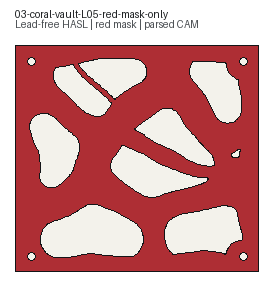
order-packages/four-art-series/current/bundle/previews/03-coral-vault-L05-red-mask-only.png
