Takazudo/zudo-blanks/order-packages/four-art-series/current/bundle/previews/03-coral-vault-L06-yellow-mask-only.png

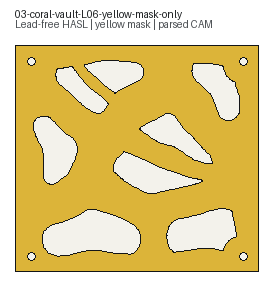
order-packages/four-art-series/current/bundle/previews/03-coral-vault-L06-yellow-mask-only.png
