Takazudo/zudo-blanks/order-packages/four-art-series/current/bundle/previews/13-fault-line-L01-black-enig-art.png

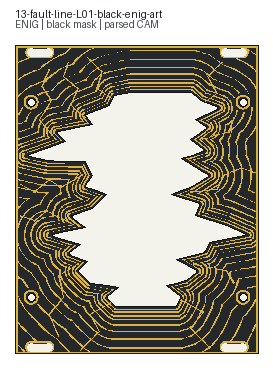
order-packages/four-art-series/current/bundle/previews/13-fault-line-L01-black-enig-art.png
