Takazudo/zudo-blanks/order-packages/four-art-series/current/bundle/previews/13-fault-line-L04-red-mask-only.png

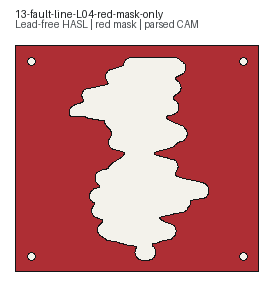
order-packages/four-art-series/current/bundle/previews/13-fault-line-L04-red-mask-only.png
