Takazudo/zudo-blanks/order-packages/four-art-series/current/bundle/previews/17-kumiko-void-wide-L01-black-enig-art.png

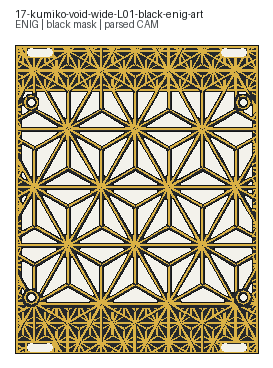
order-packages/four-art-series/current/bundle/previews/17-kumiko-void-wide-L01-black-enig-art.png
