Takazudo/zudo-blanks/order-packages/four-art-series/current/bundle/previews/17-kumiko-void-wide-L05-red-mask-only.png

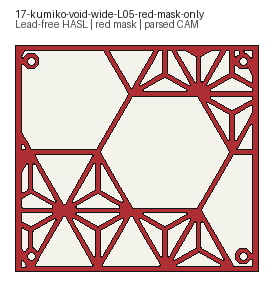
order-packages/four-art-series/current/bundle/previews/17-kumiko-void-wide-L05-red-mask-only.png
