Takazudo/zudo-blanks/order-packages/four-art-series/current/bundle/previews/nominal-stack-sides.png

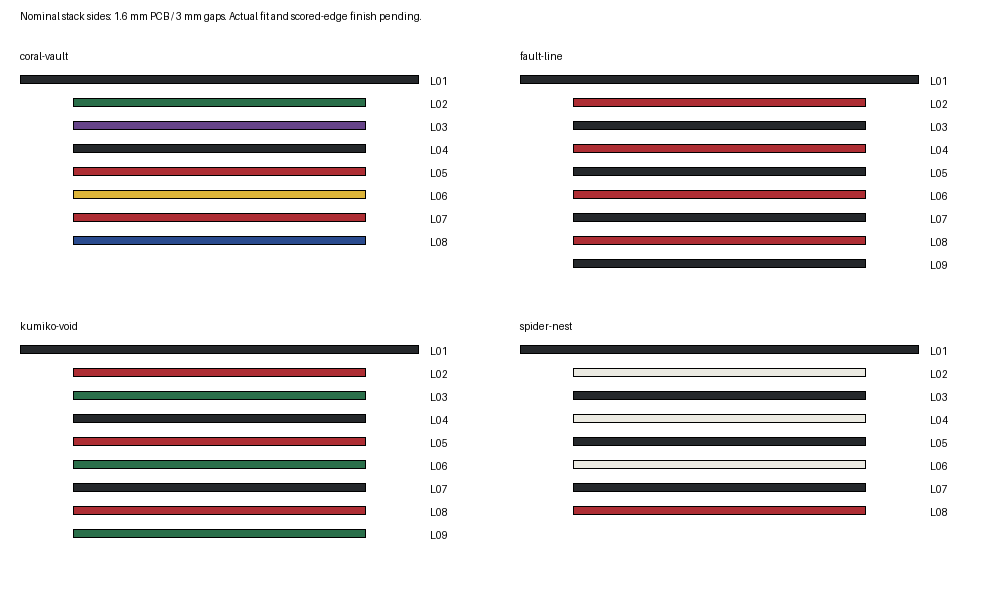
order-packages/four-art-series/current/bundle/previews/nominal-stack-sides.png
