Takazudo/zudo-blanks/order-packages/four-art-series/current/bundle/variants/grouped/lower-panel-black-enig.png

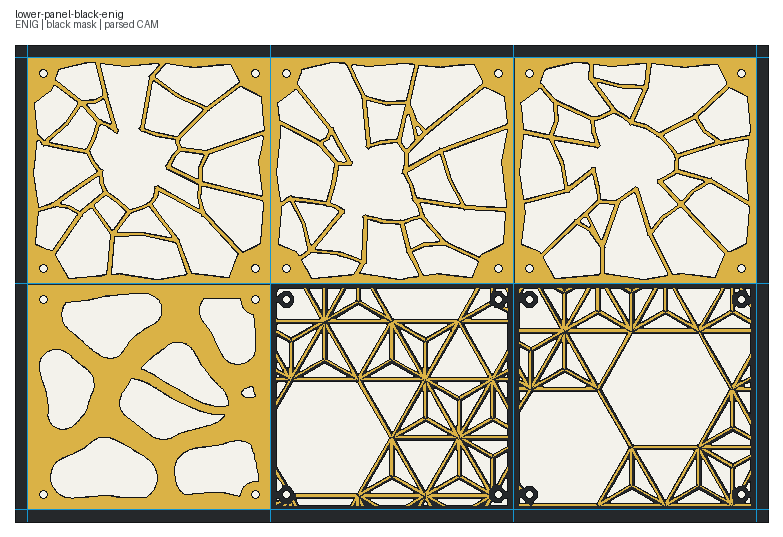
order-packages/four-art-series/current/bundle/variants/grouped/lower-panel-black-enig.png
