Takazudo/zudo-blanks/order-packages/four-art-series/current/bundle/variants/grouped/lower-panel-black-hasl.png

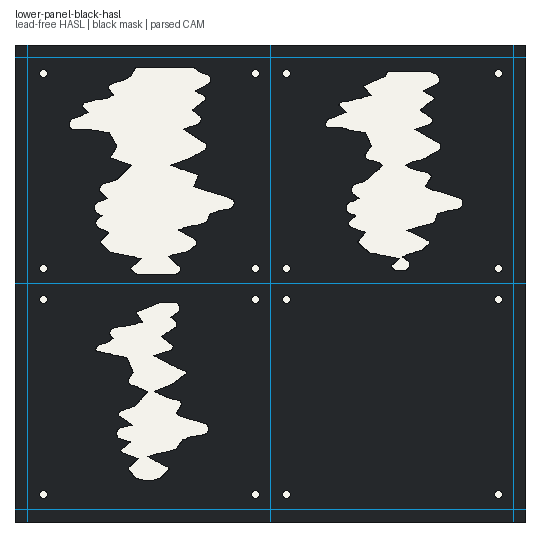
order-packages/four-art-series/current/bundle/variants/grouped/lower-panel-black-hasl.png
