Takazudo/zudo-blanks/order-packages/four-art-series/current/bundle/variants/split-red/lower-panel-red-hasl-six.png

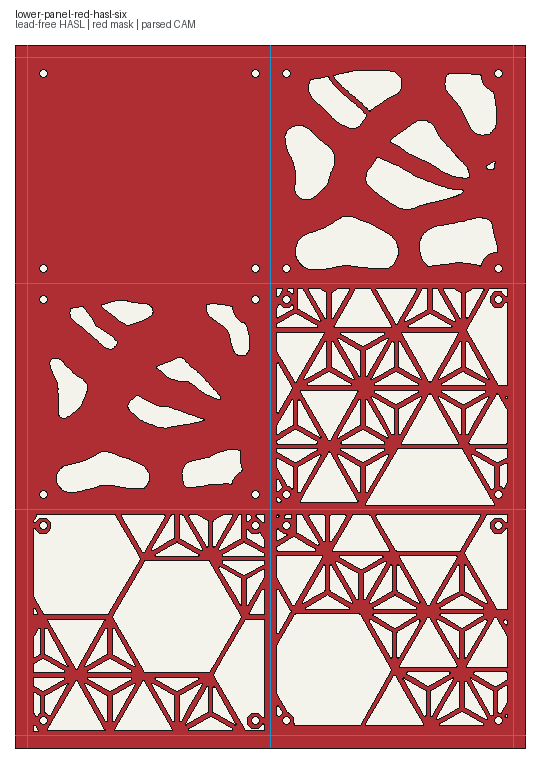
order-packages/four-art-series/current/bundle/variants/split-red/lower-panel-red-hasl-six.png
