Takazudo/zudo-blanks/artwork-resources/pcb-art/docs-overlay/src/content/docs/assembly/index.mdx

---
title: "Assembly"
description: "Eight- and nine-layer stacks, spacers, and fastener notes."
sidebar_position: 5
---

The following stack quantities are design estimates. Confirm physical hardware and case clearance before assembly.

<CategoryNav category="assembly" />
