Takazudo/zudo-blanks/artwork-resources/pcb-art/docs-overlay/src/content/docs/manufacturing/index.mdx

---
title: "Manufacturing Review"
description: "Native-board checks, process constraints, and open items."
sidebar_position: 4
---

These pages identify review work still needed before any order. They do not claim factory acceptance.

<CategoryNav category="manufacturing" />
