Takazudo/zudo-blanks/artwork-resources/pcb-art/manufacturing/candidate-detail-coral-vault-L01-middle-neck.png

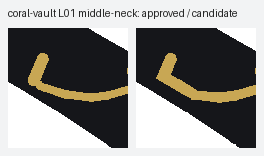
artwork-resources/pcb-art/manufacturing/candidate-detail-coral-vault-L01-middle-neck.png
