Takazudo/zudo-blanks/artwork-resources/pcb-art/manufacturing/candidate-detail-fault-line-L01-terminal-cliff.png

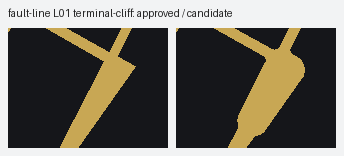
artwork-resources/pcb-art/manufacturing/candidate-detail-fault-line-L01-terminal-cliff.png
