Takazudo/zudo-blanks/artwork-resources/pcb-art/manufacturing/candidate-detail-kumiko-void-L01-top-facets.png

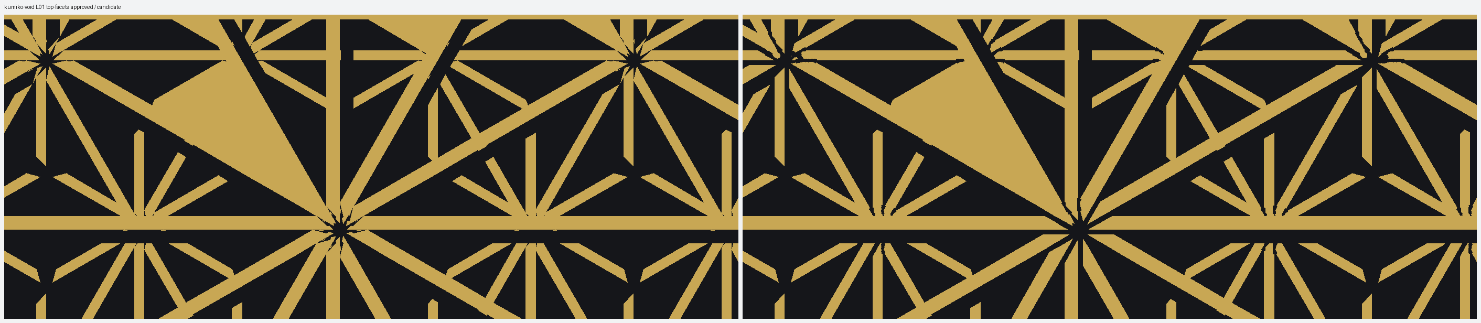
artwork-resources/pcb-art/manufacturing/candidate-detail-kumiko-void-L01-top-facets.png
