Takazudo/zudo-blanks/artwork-resources/pcb-art/manufacturing/candidate-detail-kumiko-void-L07-l07-lower.png

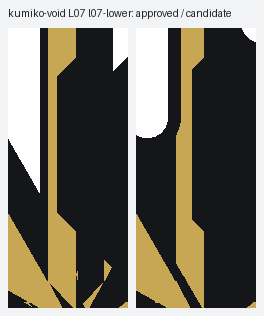
artwork-resources/pcb-art/manufacturing/candidate-detail-kumiko-void-L07-l07-lower.png
