Takazudo/zudo-blanks/artwork-resources/pcb-art/manufacturing/candidate-detail-kumiko-void-L07-l07-upper.png

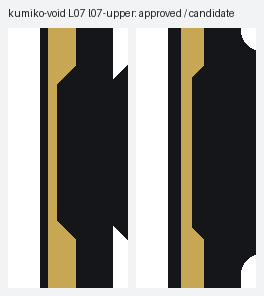
artwork-resources/pcb-art/manufacturing/candidate-detail-kumiko-void-L07-l07-upper.png
