Takazudo/zudo-blanks/artwork-resources/pcb-art/manufacturing/candidate-detail-spider-nest-L01-guide-channels.png

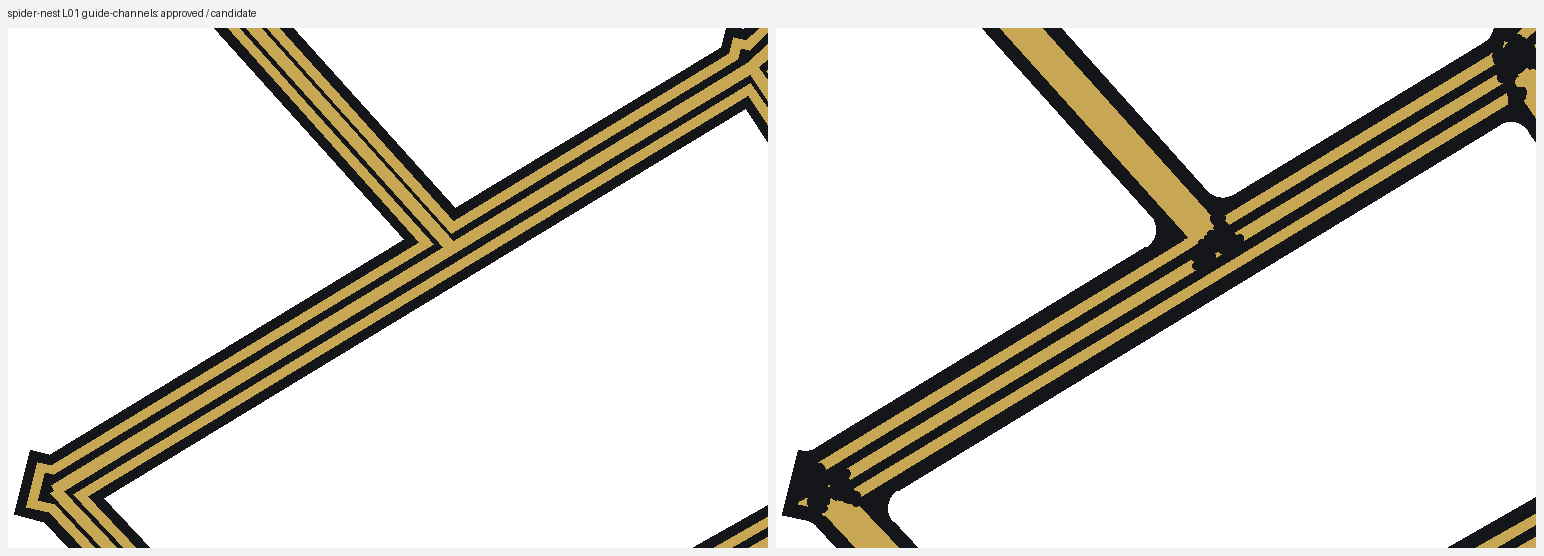
artwork-resources/pcb-art/manufacturing/candidate-detail-spider-nest-L01-guide-channels.png
