Takazudo/zudo-blanks/artwork-resources/pcb-art/manufacturing/candidate-detail-woven-maze-L01-top-maze.png

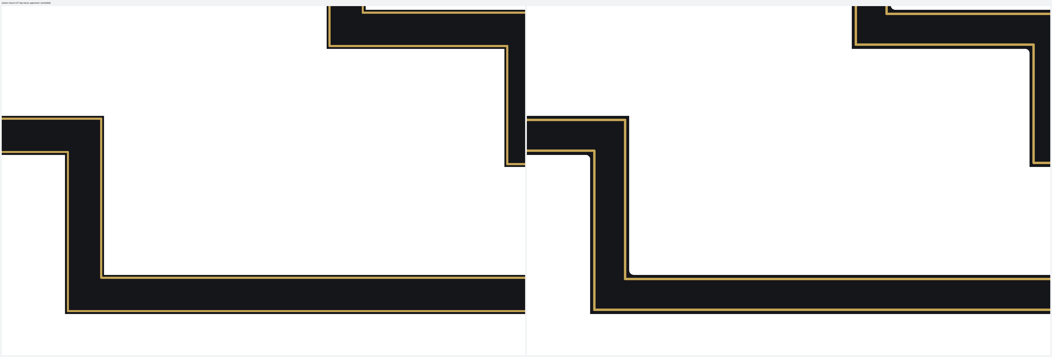
artwork-resources/pcb-art/manufacturing/candidate-detail-woven-maze-L01-top-maze.png
