Takazudo/zudo-blanks/artwork-resources/pcb-art/manufacturing/candidate-geometry-coral-vault.png

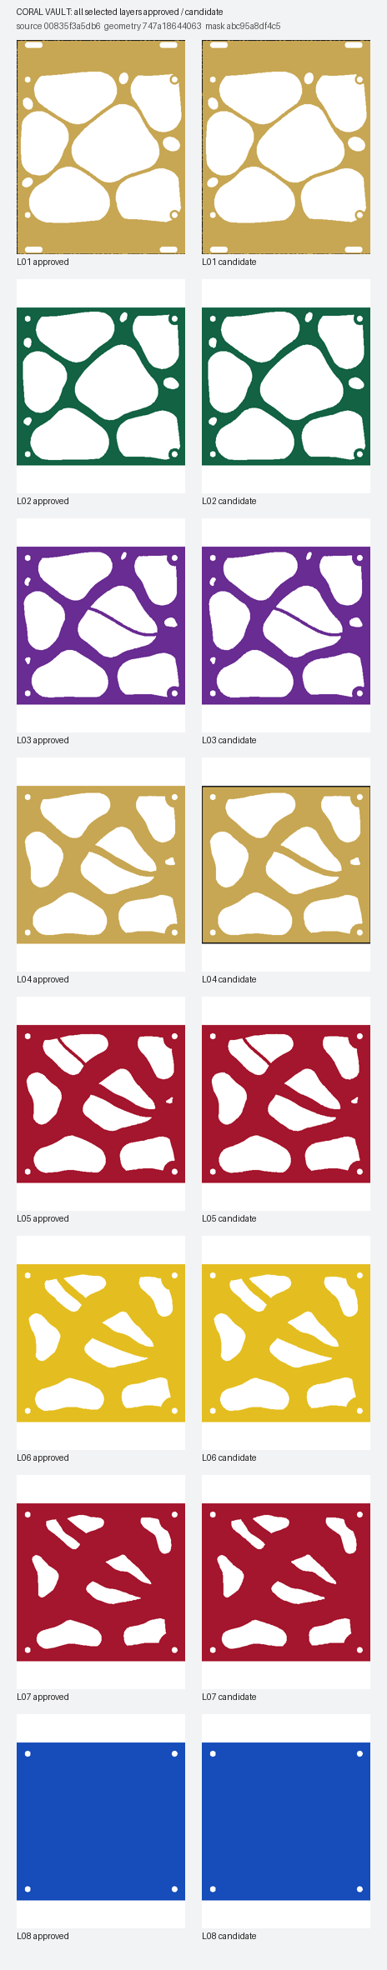
artwork-resources/pcb-art/manufacturing/candidate-geometry-coral-vault.png
