Takazudo/zudo-blanks/artwork-resources/pcb-art/manufacturing/candidate-geometry-fault-line.png

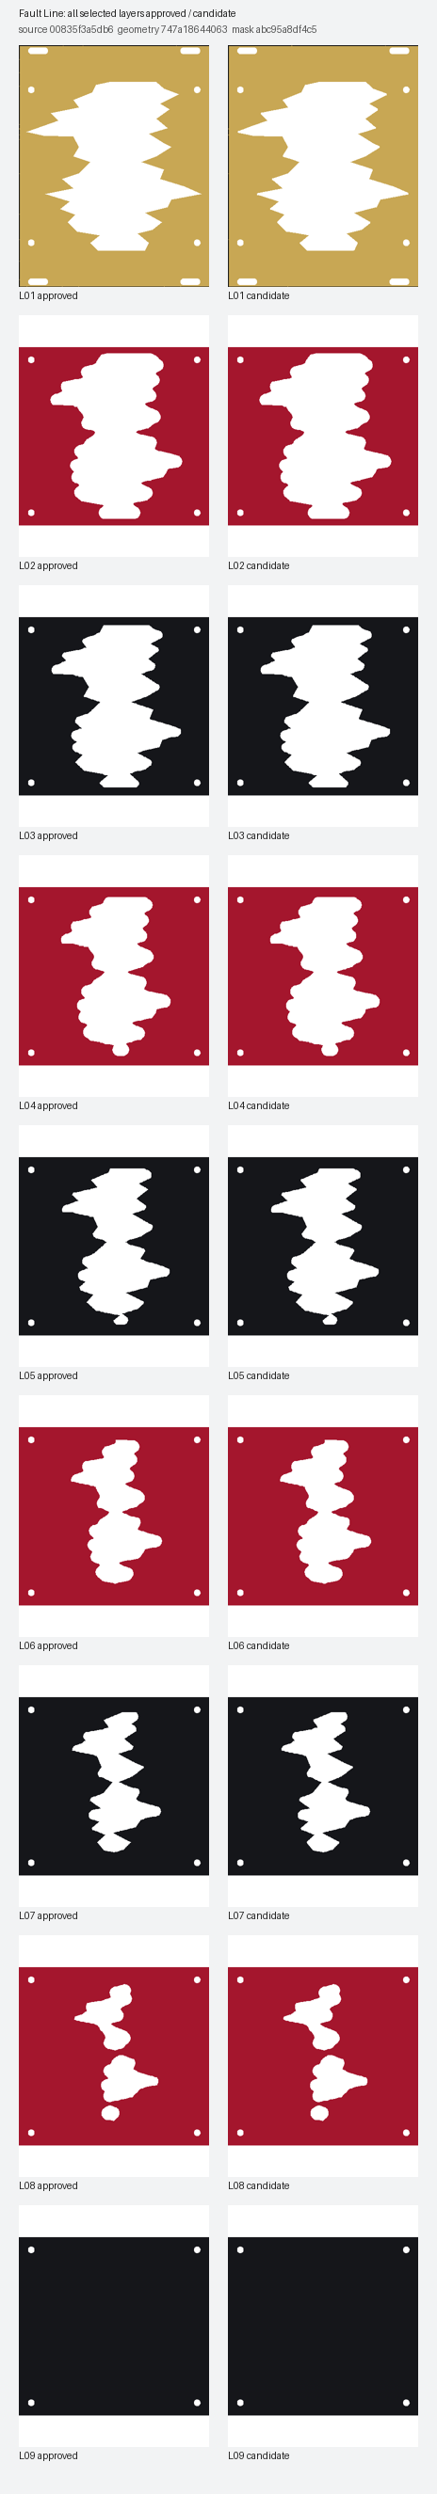
artwork-resources/pcb-art/manufacturing/candidate-geometry-fault-line.png
