Takazudo/zudo-blanks/artwork-resources/pcb-art/manufacturing/candidate-geometry-kumiko-void.png

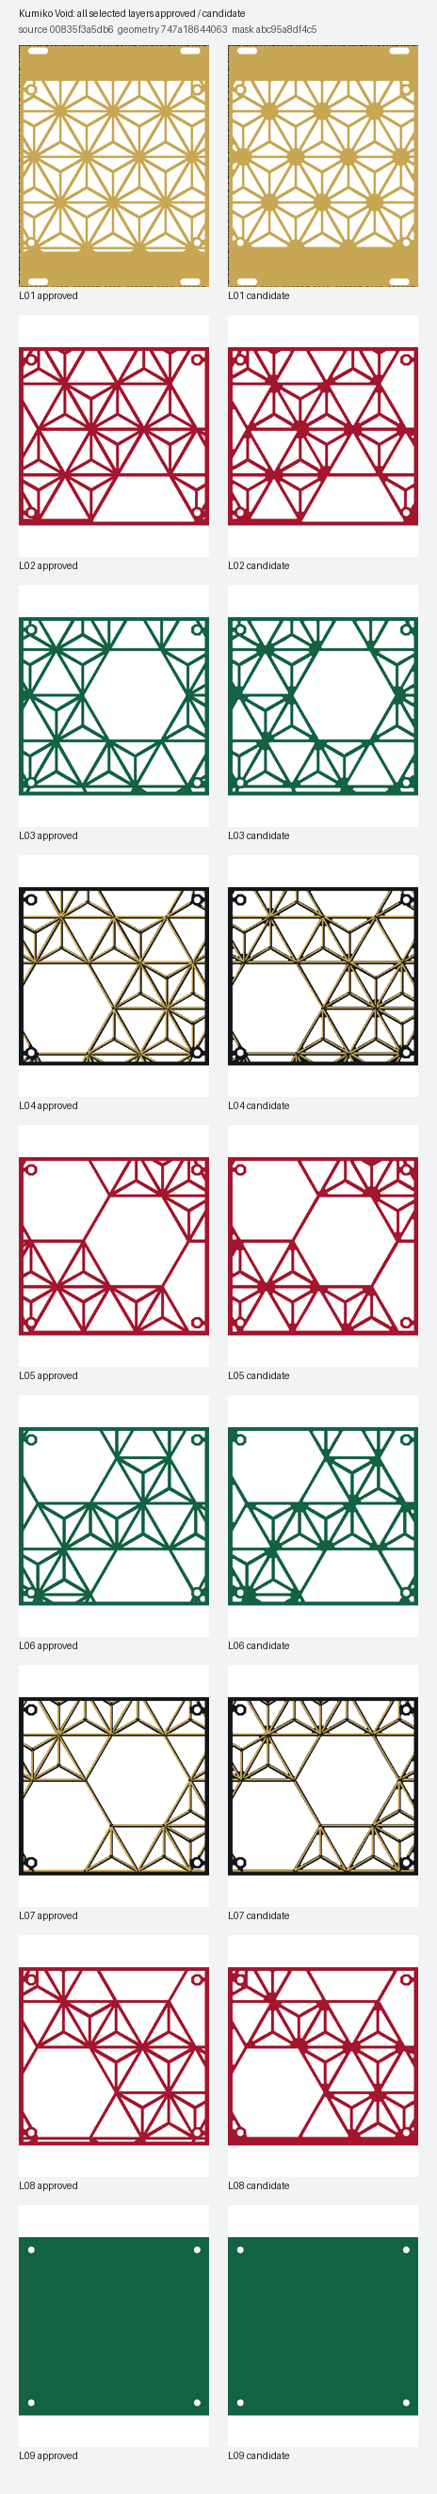
artwork-resources/pcb-art/manufacturing/candidate-geometry-kumiko-void.png
