Takazudo/zudo-blanks/artwork-resources/pcb-art/manufacturing/candidate-geometry-spider-nest.png

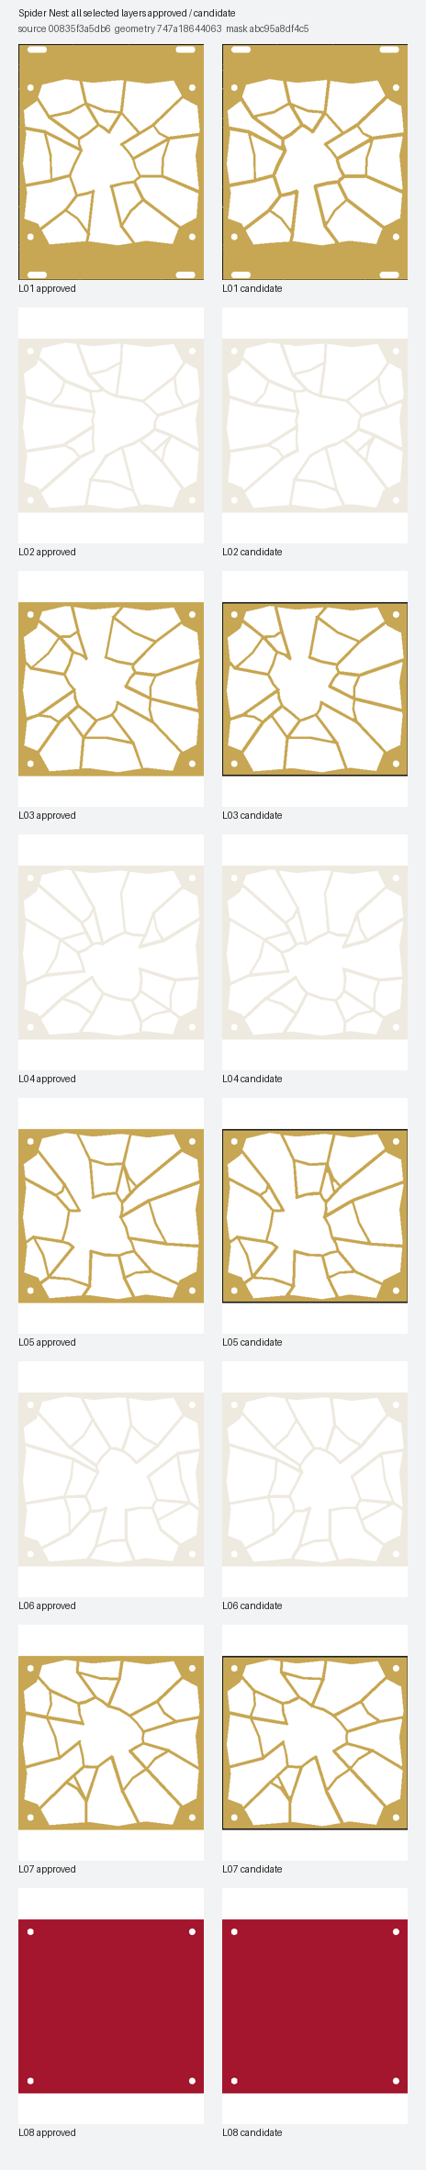
artwork-resources/pcb-art/manufacturing/candidate-geometry-spider-nest.png
