Takazudo/zudo-blanks/artwork-resources/pcb-art/manufacturing/candidate-geometry-woven-maze.png

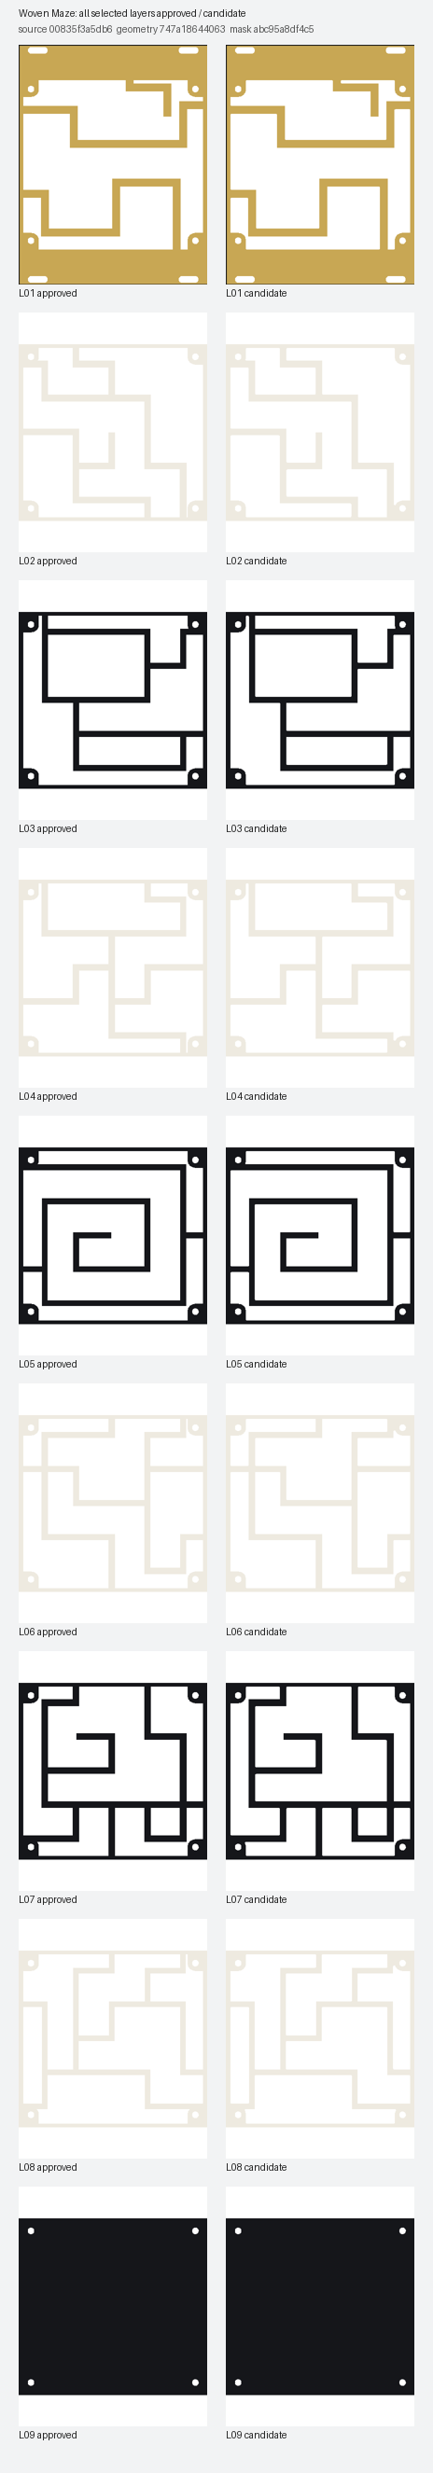
artwork-resources/pcb-art/manufacturing/candidate-geometry-woven-maze.png
