Takazudo/zudo-blanks/artwork-resources/pcb-art/manufacturing/decision-comparisons.png

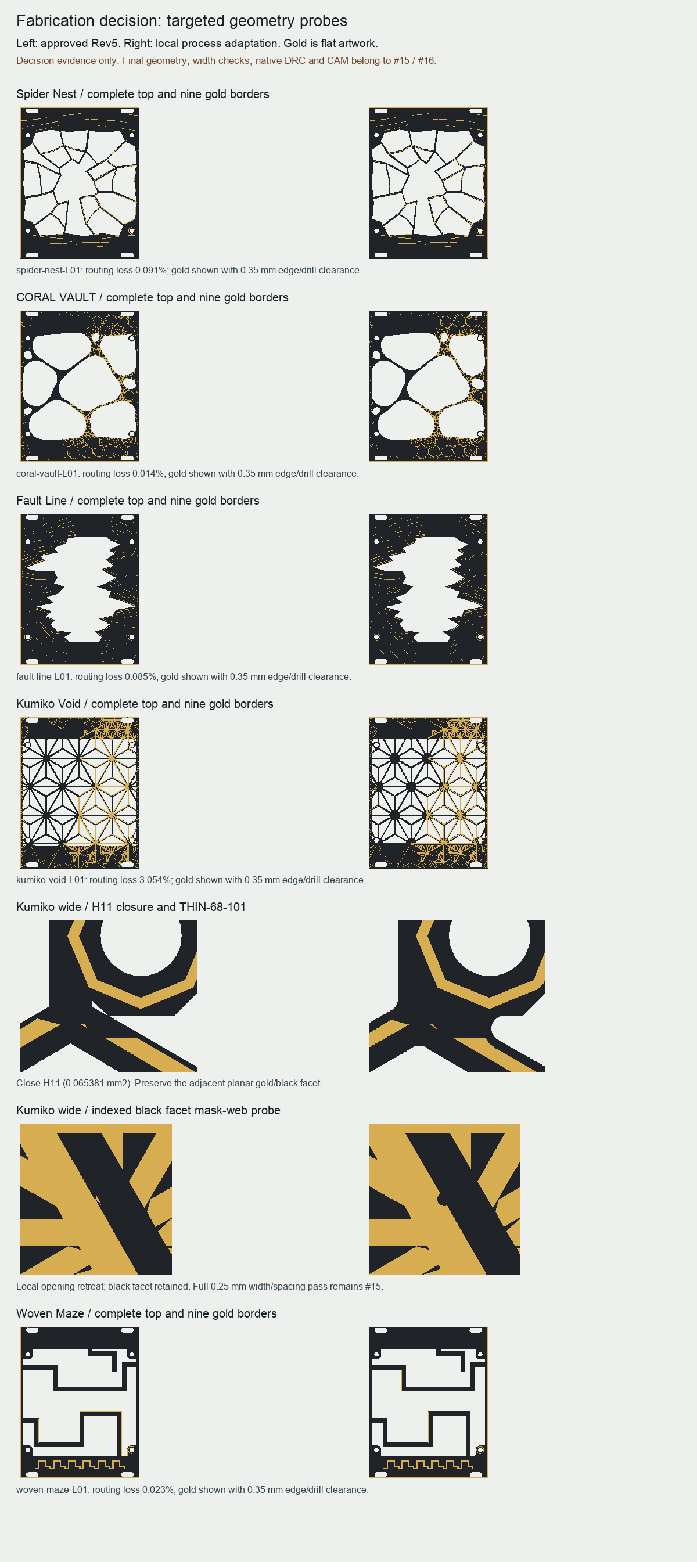
artwork-resources/pcb-art/manufacturing/decision-comparisons.png
