Takazudo/zudo-blanks/artwork-resources/pcb-art/manufacturing/process-class-comparison.png

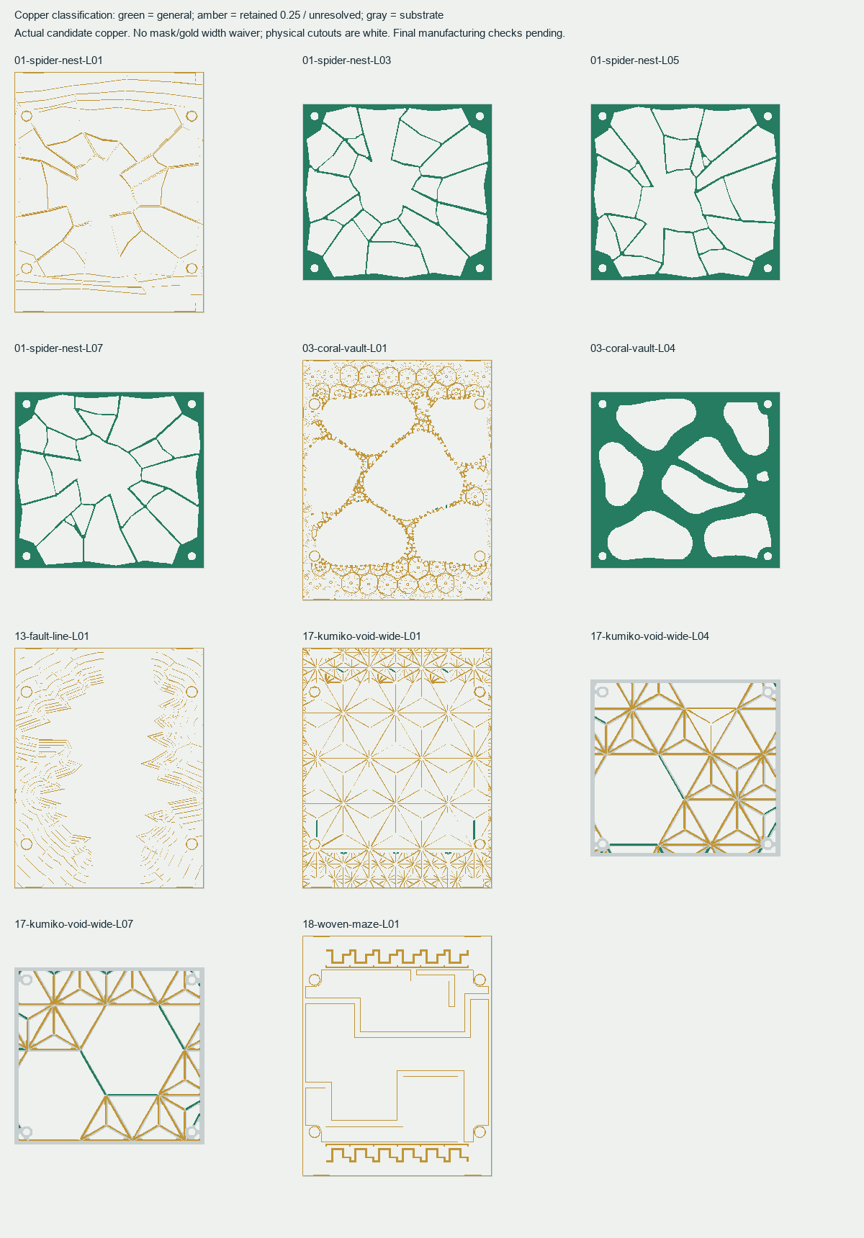
artwork-resources/pcb-art/manufacturing/process-class-comparison.png
