Takazudo/zudo-blanks/artwork-resources/pcb-art/manufacturing/spider-channel-erratum.png

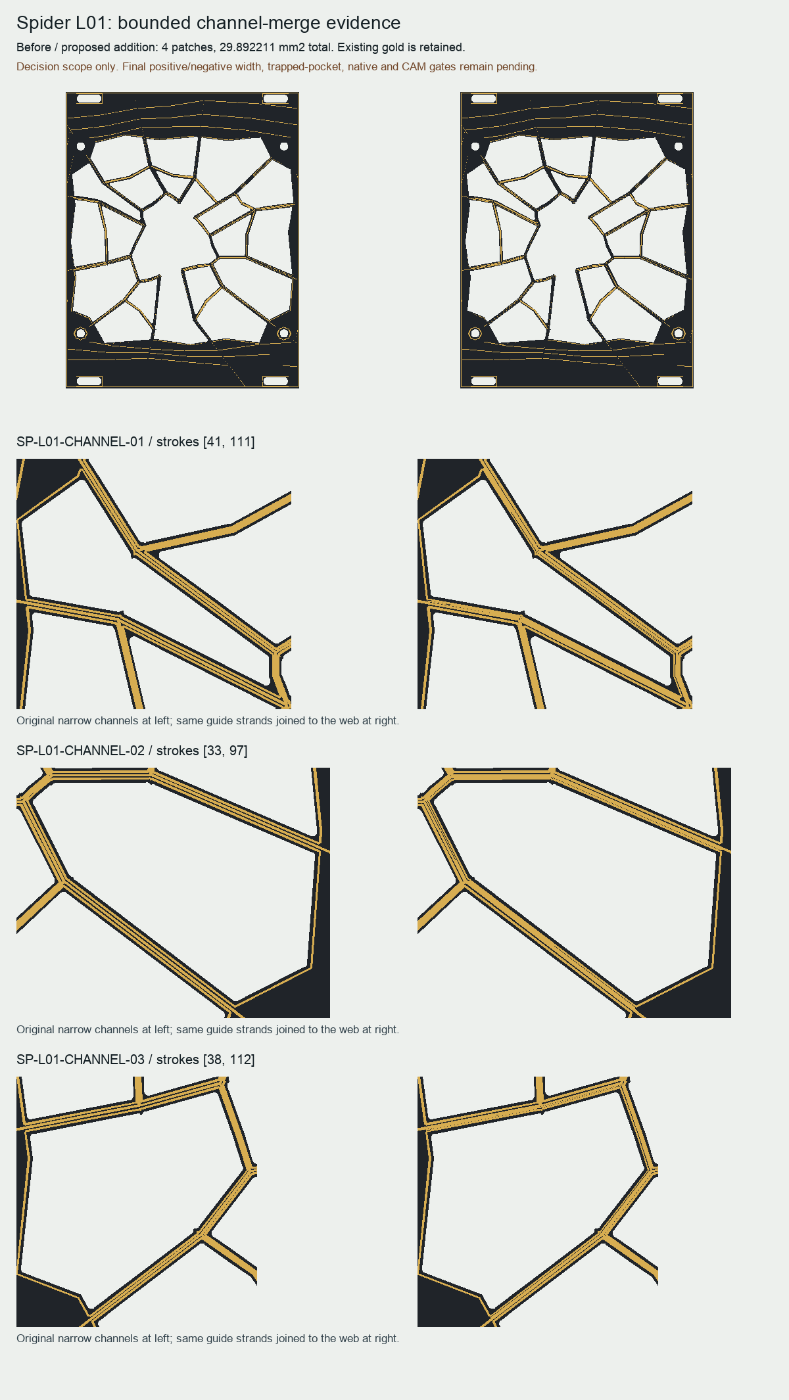
artwork-resources/pcb-art/manufacturing/spider-channel-erratum.png
