Takazudo/zudo-blanks/artwork-resources/pcb-art/manufacturing/spider-complete-comparison.png

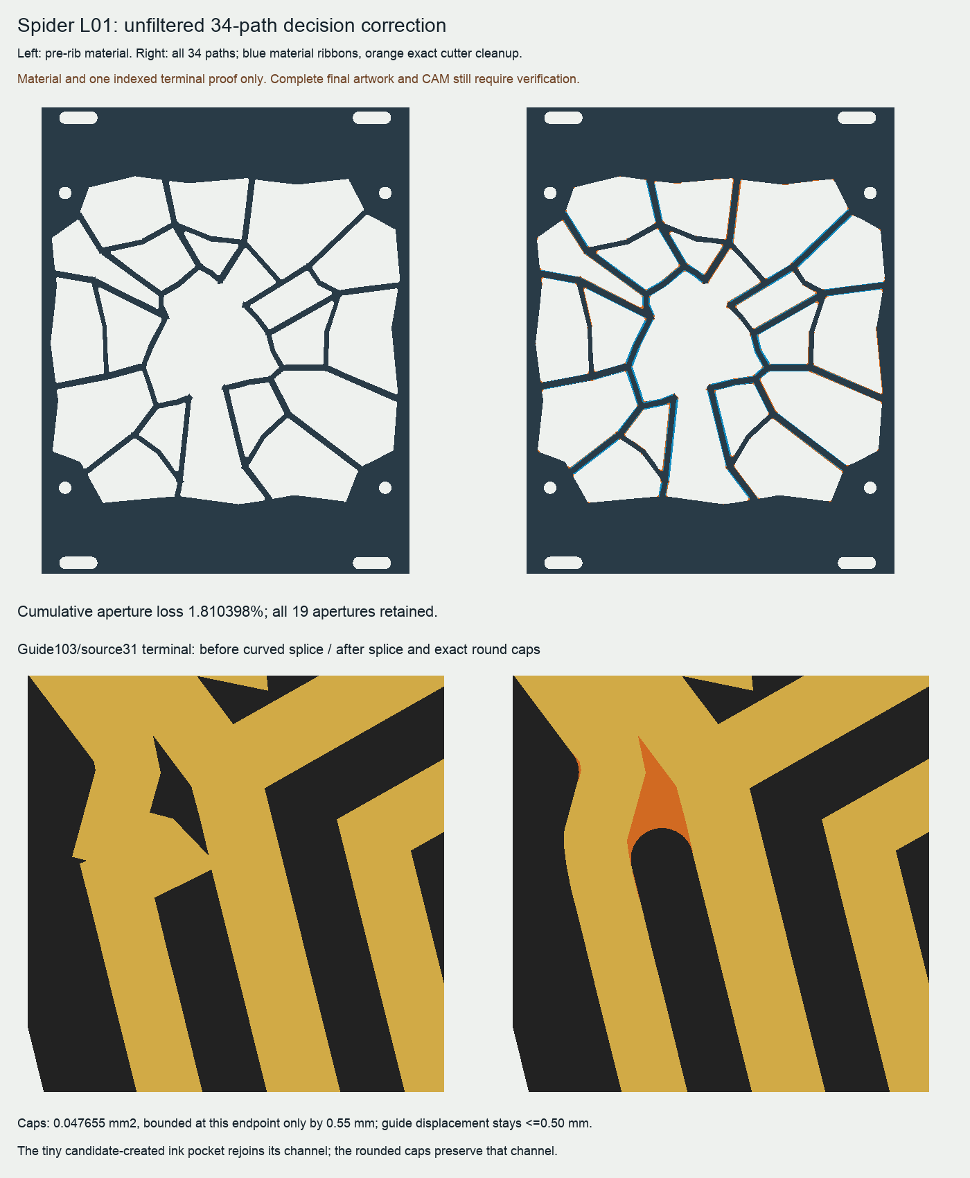
artwork-resources/pcb-art/manufacturing/spider-complete-comparison.png
