Takazudo/zudo-blanks/artwork-resources/pcb-art/manufacturing/spider-network-comparison.png

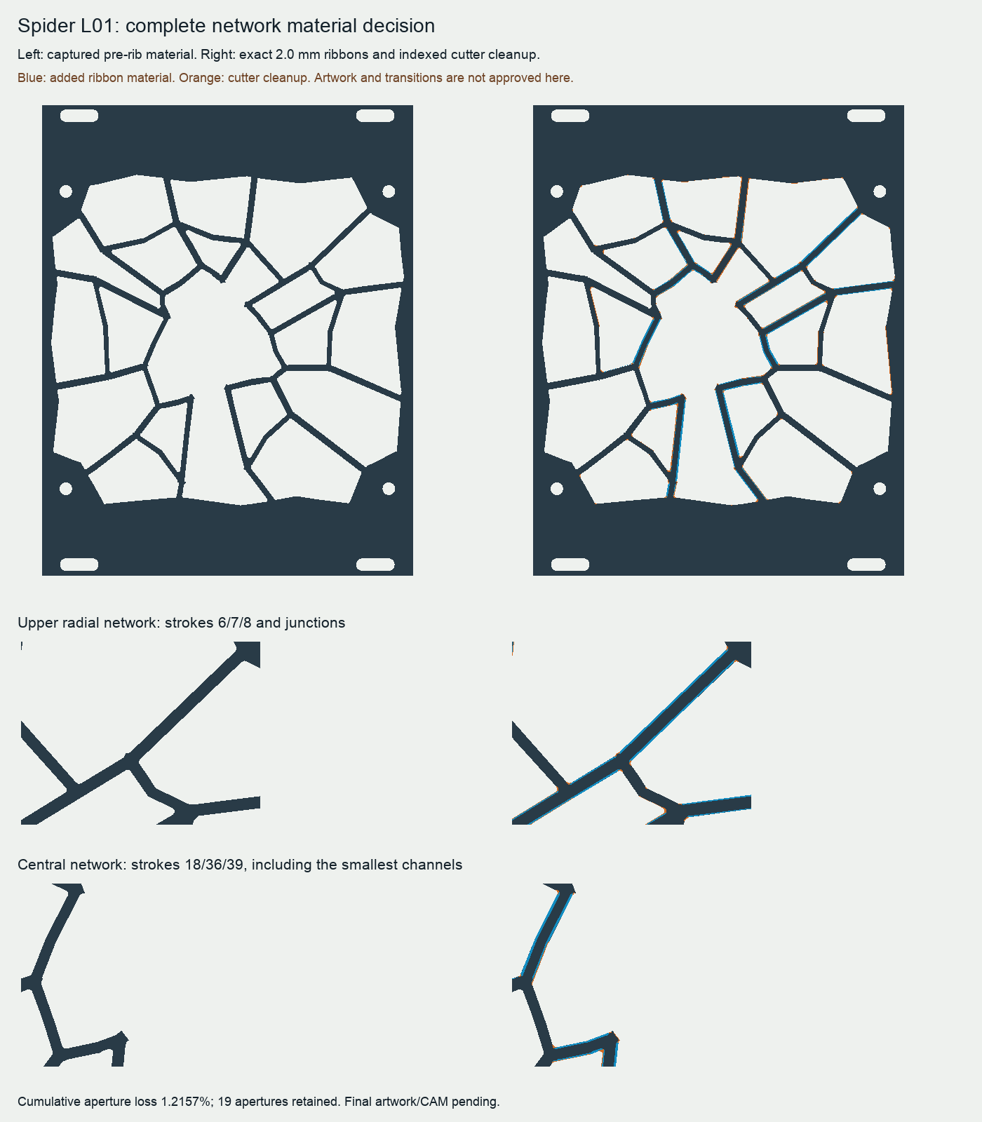
artwork-resources/pcb-art/manufacturing/spider-network-comparison.png
