Takazudo/zudo-blanks/artwork-resources/pcb-art/manufacturing/spider-rib-comparison.png

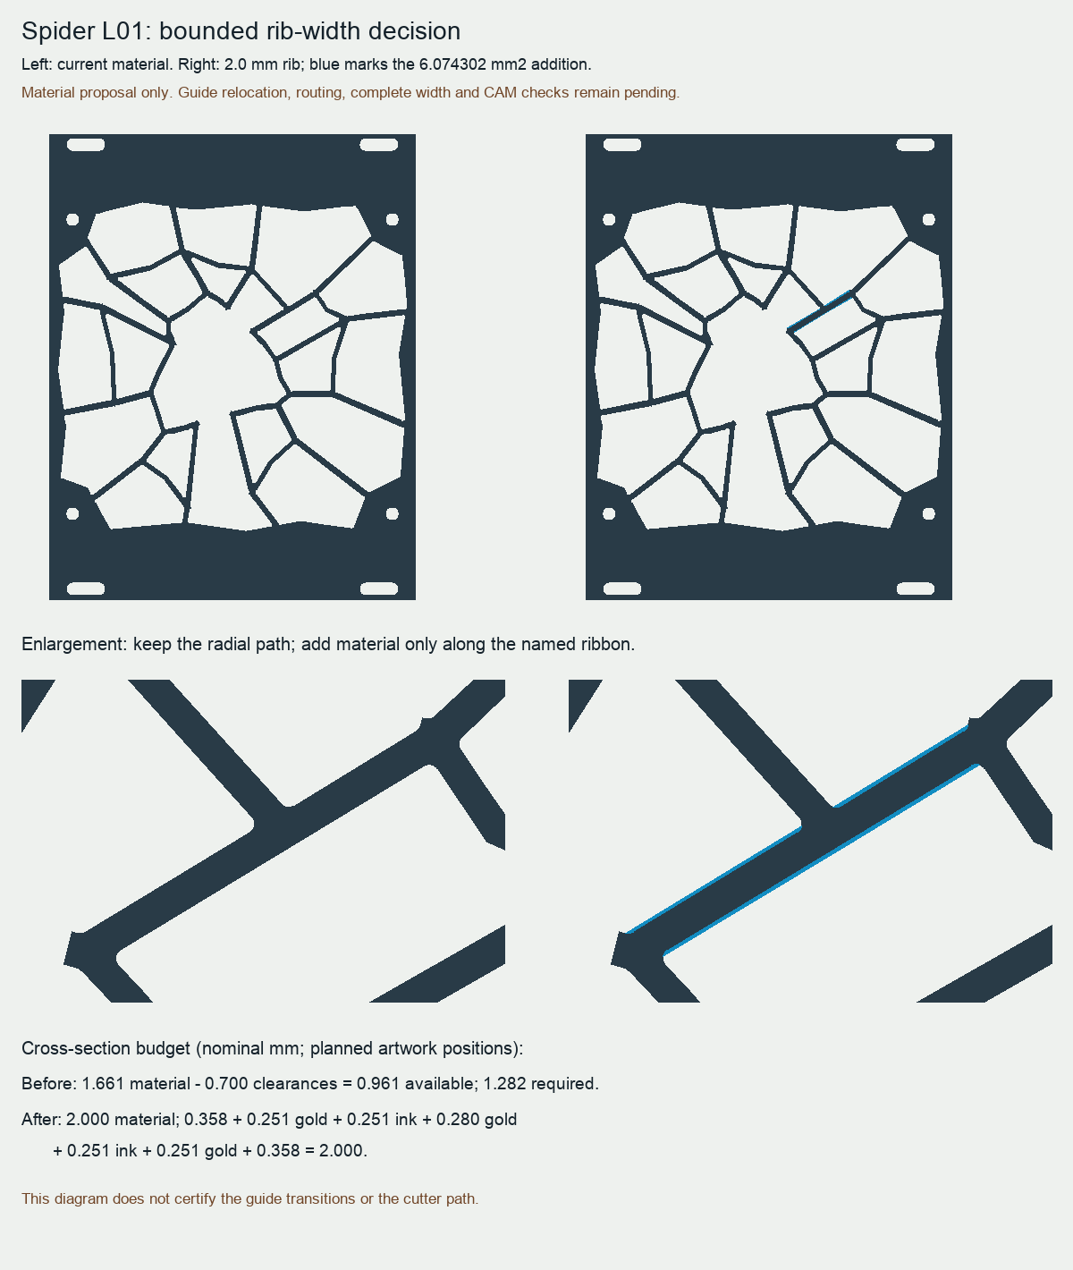
artwork-resources/pcb-art/manufacturing/spider-rib-comparison.png
