Takazudo/zudo-blanks/order-packages/four-art-series/current/bundle/inputs/artwork-resources/pcb-art/manufacturing/audit_art_candidate.py

#!/usr/bin/env python3
"""Index inherited pairwise art findings against the corrected geometry candidate.

This is a diagnostic inventory. A covered midpoint is not a printable-width
proof, and an open midpoint is not automatically a finished-union violation.
"""
import hashlib
import importlib.util
import json
from pathlib import Path

from shapely.geometry import Point, Polygon, LineString
from shapely.ops import unary_union, nearest_points
from shapely.strtree import STRtree

HERE = Path(__file__).resolve().parent
ROOT = HERE.parent
spec = importlib.util.spec_from_file_location('export_reference',ROOT/'tools/export_kicad.py')
export = importlib.util.module_from_spec(spec)
spec.loader.exec_module(export)


def sha(path):
    return hashlib.sha256(path.read_bytes()).hexdigest()


def safe_region(layer,body,art_layer):
    safe=body.buffer(-(.35 if art_layer=='mask' else .30),quad_segs=64)
    if layer['index']>0:
        safe=safe.intersection(Polygon(layer['outer']).buffer(
            -(.55 if art_layer=='mask' else .50),join_style='mitre'))
    return safe


def union_pairs(board_id, feature, geom, input_hash):
    """Screen distinct finished positive-region components at the frozen 0.25 mm rule."""
    parts=export.ordered(geom)
    tree=STRtree(parts)
    found=[]
    for i,p in enumerate(parts):
        for j in tree.query(p.buffer(.25)):
            j=int(j)
            if j<=i:
                continue
            gap=p.distance(parts[j])
            if gap>=.25-.000001:
                continue
            a,b=nearest_points(p,parts[j])
            found.append({
                'key':f'art:{input_hash}:{board_id}:{feature}:{i}:{j}',
                'boardId':board_id,'feature':feature,
                'finishedUnionPolygonIndices0':[i,j],
                'gapMm':round(gap,9),
                'closestPointsMm':[[round(a.x,9),round(a.y,9)],
                                   [round(b.x,9),round(b.y,9)]],
                'disposition':'unresolved; diagnostic pair below 0.25 mm',
            })
    return found


def run():
    data = json.loads((HERE/'manufacturing-geometry.json').read_text())
    review = json.loads((ROOT/'validation/export-art-review.json').read_text())
    records = []
    finished = []
    subwidth = []
    summary = {}
    input_hash=sha(HERE/'manufacturing-geometry.json')
    for family in data['designs']:
        design = (next(d for d in family['variants'] if d.get('variantId')=='wide')
                  if family['id']=='kumiko-void' else family)
        for layer in design['layers']:
            finding = next(b for b in review['boards'] if b['designId']==design['id']
                           and b['layerNumber']==layer['index']+1
                           and b.get('variant')==design.get('variantId'))
            if layer['finish']=='mask-only':
                assert not finding['copperGapsBelow010Mm'] and not finding['blackMaskGapsBelow013Mm']
                continue
            drills=export.drill_specs(layer,data['spec'])
            cutouts=export.split_functional_holes(layer,drills)
            body=Polygon(layer['outer']).difference(unary_union(cutouts)).difference(
                unary_union([export.drill_shape(d) for d in drills]))
            gold=export.paint_gold(layer,design,body)
            mask=gold.intersection(safe_region(layer,body,'mask'))
            copper_safe=safe_region(layer,body,'copper')
            copper=mask.buffer(.05,quad_segs=64).intersection(copper_safe)
            copper_pairs=union_pairs(finding['boardId'],'F.Cu island gap',copper,input_hash)
            for pair in copper_pairs:
                envelope=LineString(pair['closestPointsMm']).buffer(.125,quad_segs=64)
                outside=envelope.difference(copper_safe).area
                pair['straight025MmJoinOutsideSafeAreaMm2']=round(outside,9)
                pair['straight025MmJoinFitsCopperSafeRegion']=outside<=.00001
            mask_pairs=union_pairs(finding['boardId'],'F.Mask black gap',mask,input_hash)
            finished.extend(copper_pairs)
            finished.extend(mask_pairs)
            for index,part in enumerate(export.ordered(mask)):
                if part.buffer(-.125,quad_segs=64).is_empty:
                    subwidth.append({
                        'key':f'art:{input_hash}:{finding["boardId"]}:F.Mask no 0.25 mm disk:{index}',
                        'boardId':finding['boardId'],
                        'finishedUnionPolygonIndex0':index,
                        'boundsMm':[round(v,6) for v in part.bounds],
                        'areaMm2':round(part.area,9),
                        'disposition':'unresolved; necessary width condition fails',
                    })
            for key,feature,union in [('copperGapsBelow010Mm','F.Cu island gap',copper),
                                      ('blackMaskGapsBelow013Mm','F.Mask black gap',mask)]:
                for issue in finding[key]:
                    a,b=issue['closestPointsMm']
                    mid=Point((a[0]+b[0])/2,(a[1]+b[1])/2)
                    records.append({
                        'key':f'art:{finding["sourceSha256"]}:{finding["boardId"]}:{feature}:{issue["polygonIndices0"][0]}:{issue["polygonIndices0"][1]}',
                        'boardId':finding['boardId'],
                        'sourceExportSha256':finding['sourceSha256'],
                        'feature':feature,
                        'polygonIndices0':issue['polygonIndices0'],
                        'originalClosestPointsMm':issue['closestPointsMm'],
                        'originalGapMm':issue['gapMm'],
                        'candidateMidpointCoveredByUnion':union.covers(mid),
                        'disposition':'unresolved; finished union width/gap proof required',
                    })
            summary[finding['boardId']] = {
                'originalCopperPairFindings':len(finding['copperGapsBelow010Mm']),
                'originalMaskPairFindings':len(finding['blackMaskGapsBelow013Mm']),
                'candidateGoldAreaMm2':round(mask.area,6),
                'candidateCopperAreaMm2':round(copper.area,6),
                'finishedUnionCopperPairsBelow025Mm':len(copper_pairs),
                'straight025MmCopperJoinsOutsideSafeRegion':sum(
                    not pair['straight025MmJoinFitsCopperSafeRegion'] for pair in copper_pairs),
                'finishedUnionMaskPairsBelow025Mm':len(mask_pairs),
                'finishedMaskComponentsWithout025MmDisk':sum(
                    item['boardId']==finding['boardId'] for item in subwidth),
            }
    report={
        'status':'diagnostic only; all original selected art findings remain unresolved',
        'geometrySha256':sha(HERE/'manufacturing-geometry.json'),
        'sourceReviewSha256':sha(ROOT/'validation/export-art-review.json'),
        'summary':summary,
        'findings':records,
        'finishedUnionPairs':finished,
        'necessaryWidthFailures':subwidth,
    }
    (HERE/'art-candidate-audit.json').write_text(json.dumps(report,indent=2)+'\n')
    print(json.dumps({'selectedOriginalArtFindings':len(records),
                      'finishedUnionPairsBelow025Mm':len(finished),
                      'necessaryWidthFailures':len(subwidth),
                      'coveredMidpoints':sum(r['candidateMidpointCoveredByUnion'] for r in records)}))


if __name__=='__main__':
    run()
